kamilkurach/mrburger/resources/IMG_20240722_085424.jpg

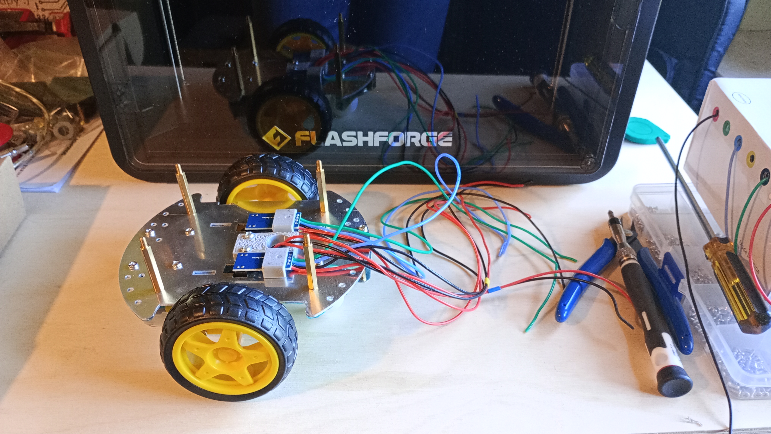
resources/IMG_20240722_085424.jpg
