kamilkurach/mrburger/resources/IMG_20240728_142720.jpg

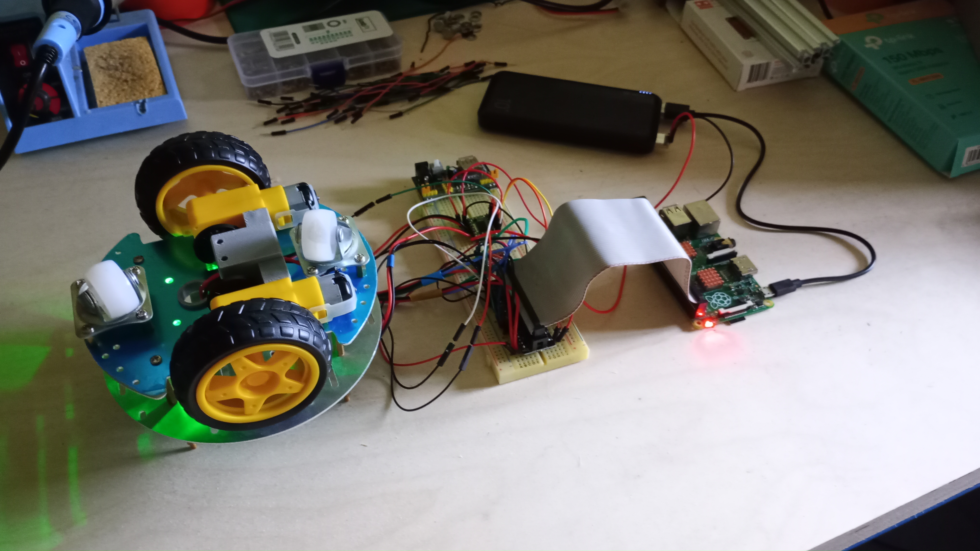
resources/IMG_20240728_142720.jpg
