kamilkurach/mrburger/resources/IMG_20240803_034906_3.jpg

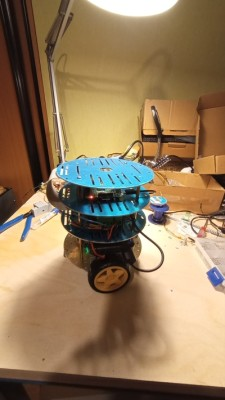
resources/IMG_20240803_034906_3.jpg
