kamilkurach/mrburger/resources/IMG_20240809_184807.jpg

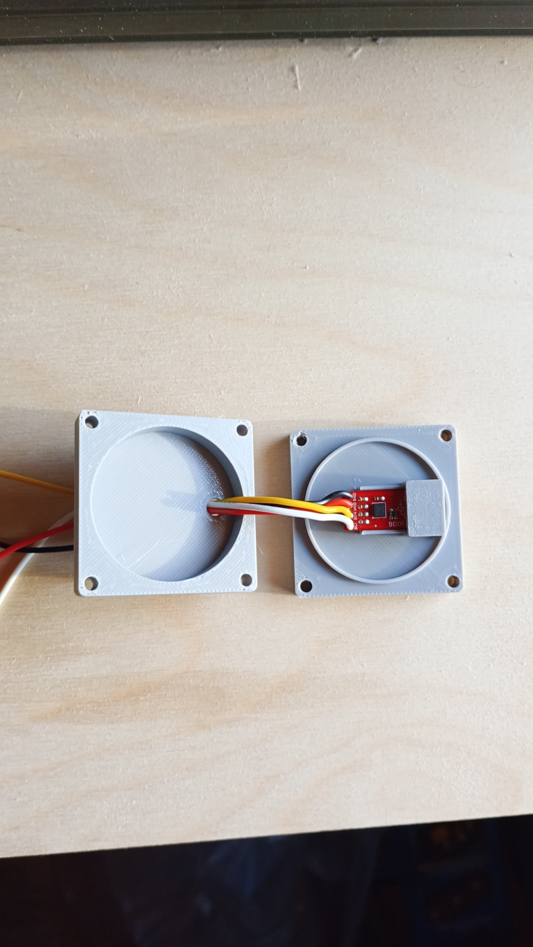
resources/IMG_20240809_184807.jpg
