kamilkurach/mrburger/resources/IMG_20241116_030415.jpg

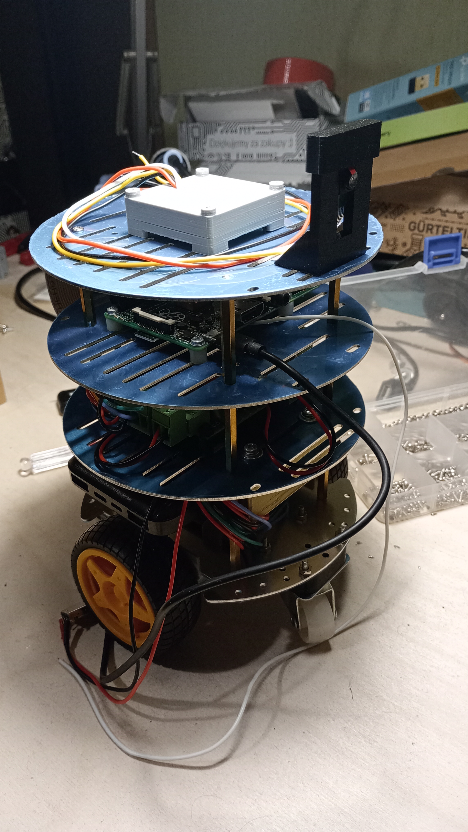
resources/IMG_20241116_030415.jpg
