kamilkurach/mrburger/resources/IMG_20241204_015451.jpg

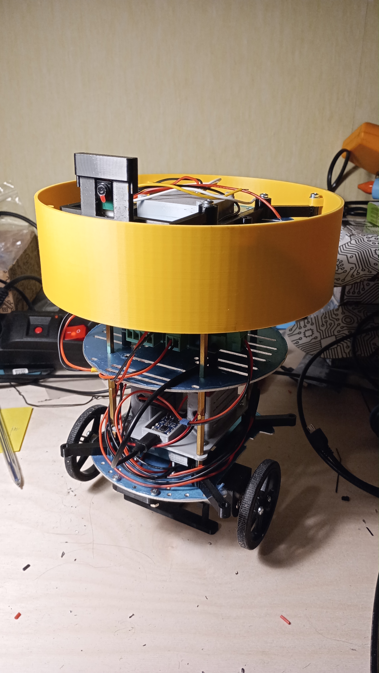
resources/IMG_20241204_015451.jpg
