kamilkurach/mrburger/resources/IMG_20241213_023858.jpg

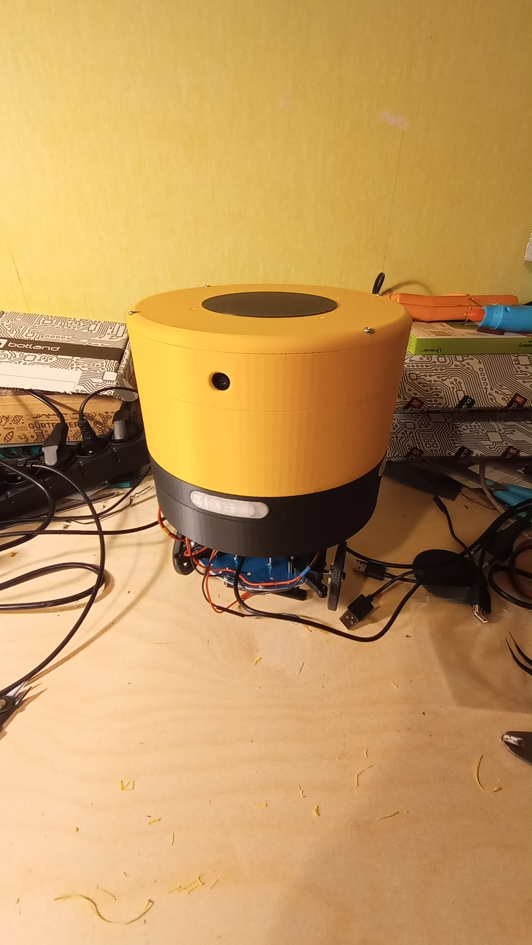
resources/IMG_20241213_023858.jpg
