kamilkurach/mrburger/resources/IMG_20241213_090648.jpg

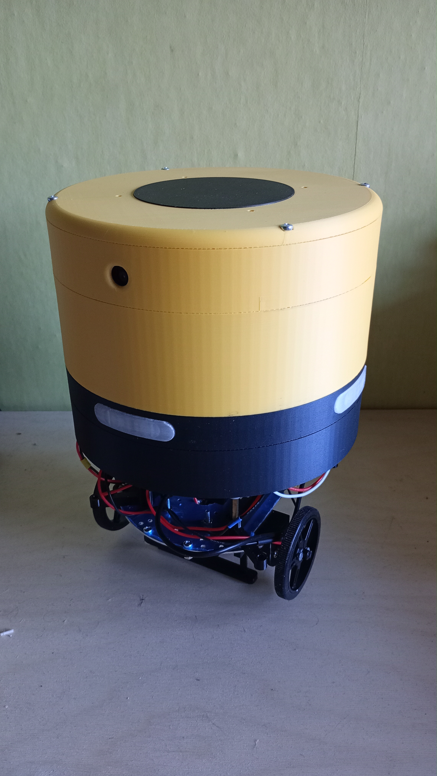
resources/IMG_20241213_090648.jpg
