kamilkurach/mrburger/stl/mrburger_induction_coil_bracket_coil_cover.stl

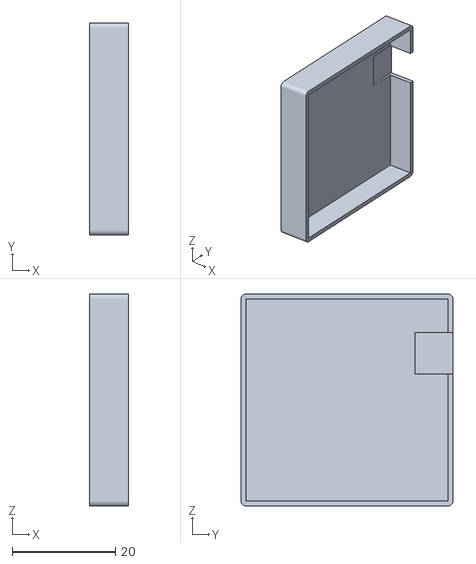
[picture p26: CAD file, 2024-12-05]
stl/mrburger_induction_coil_bracket_coil_cover.stl
7.50 x 41.0 x 41.0
