kamilkurach/mrburger/freecad/mrburger_bottom_hat.FCStd

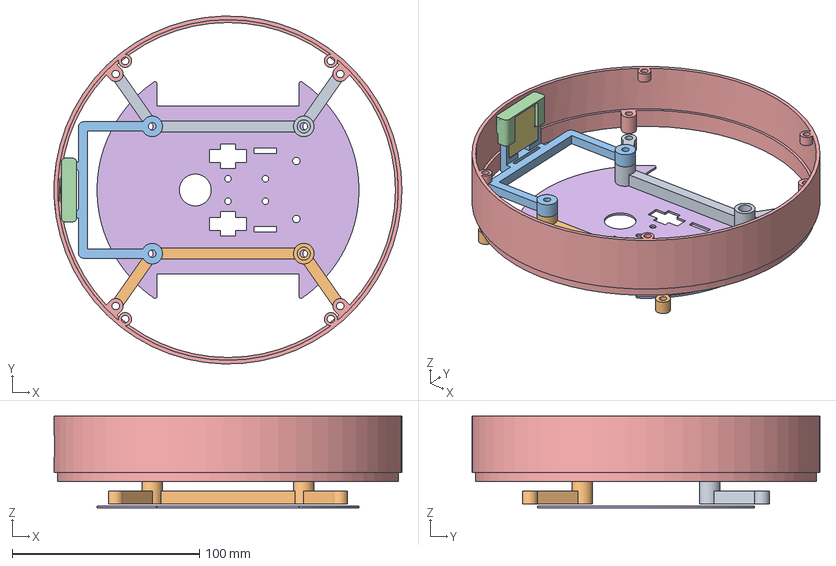
[picture p27: CAD file, 2024-12-08]
freecad/mrburger_bottom_hat.FCStd
186.0 x 185.9 x 49.0 mm
bracket
bracket_2
camera_bracket
clip
bottom_hat
mrburger_bottom_plate
mrburger_camera_module
