kamilkurach/mrburger/stl/mrburger_induction_coil_bracket_electronics_cover.stl

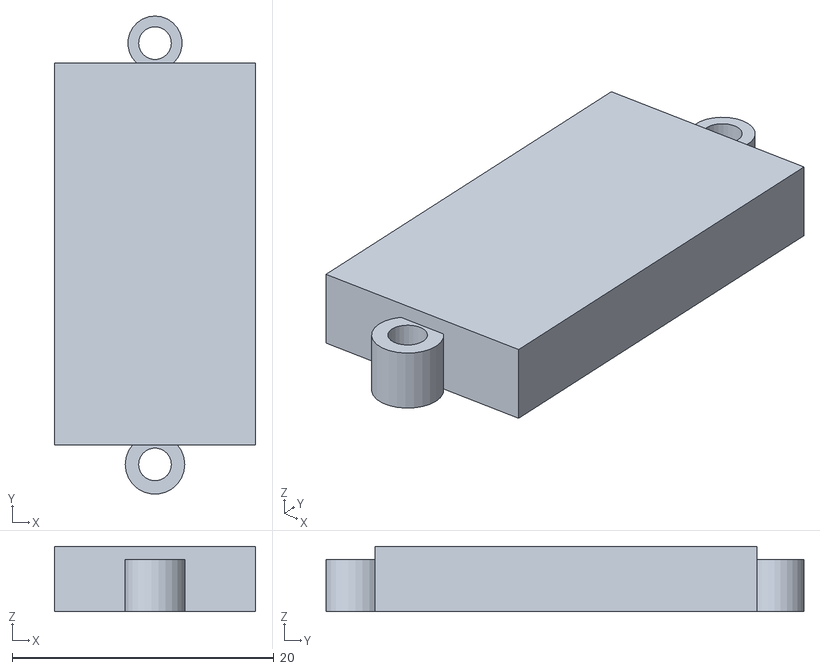
[picture p28: CAD file, 2024-12-05]
stl/mrburger_induction_coil_bracket_electronics_cover.stl
15.4 x 36.5 x 5.00
