kamilkurach/mrburger/freecad/mrburger_mid_ring.FCStd

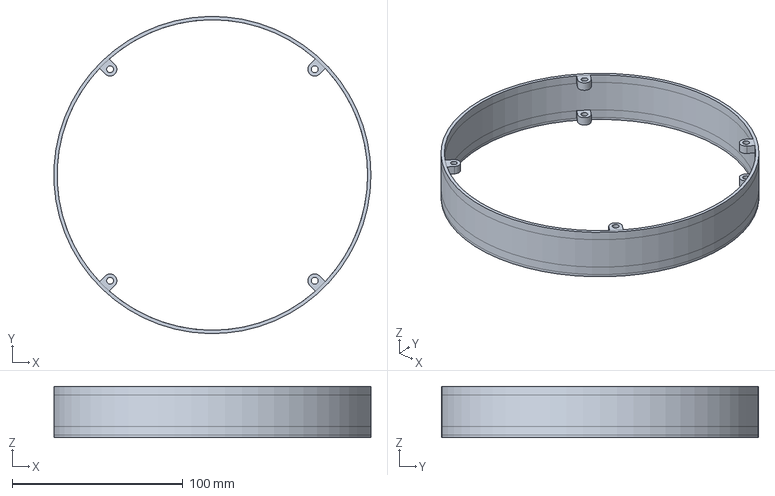
[picture p29: CAD file, 2024-12-06]
freecad/mrburger_mid_ring.FCStd
185.9 x 185.9 x 30.0 mm
