kamilkurach/mrburger/stl/mrburger_induction_coil_bracket_distance_tube.stl

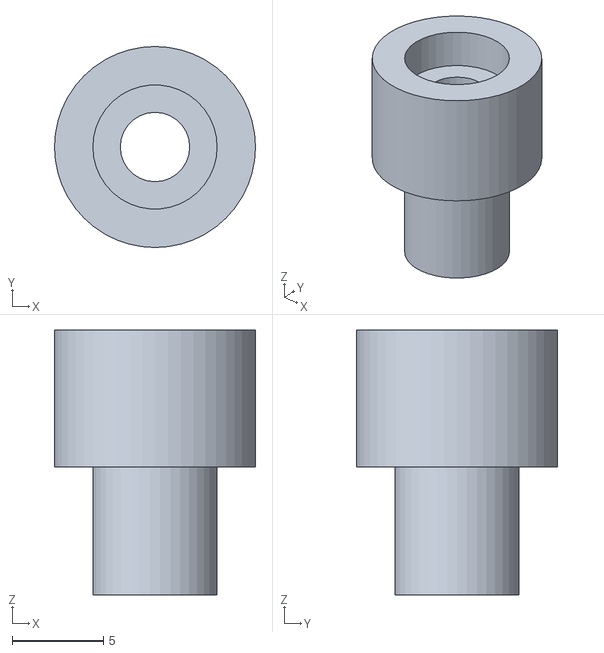
[picture p30: CAD file, 2024-12-05]
stl/mrburger_induction_coil_bracket_distance_tube.stl
11.0 x 11.0 x 14.5
