kamilkurach/mrburger/freecad/mrburger_induction_coil_bracke_2.FCStd

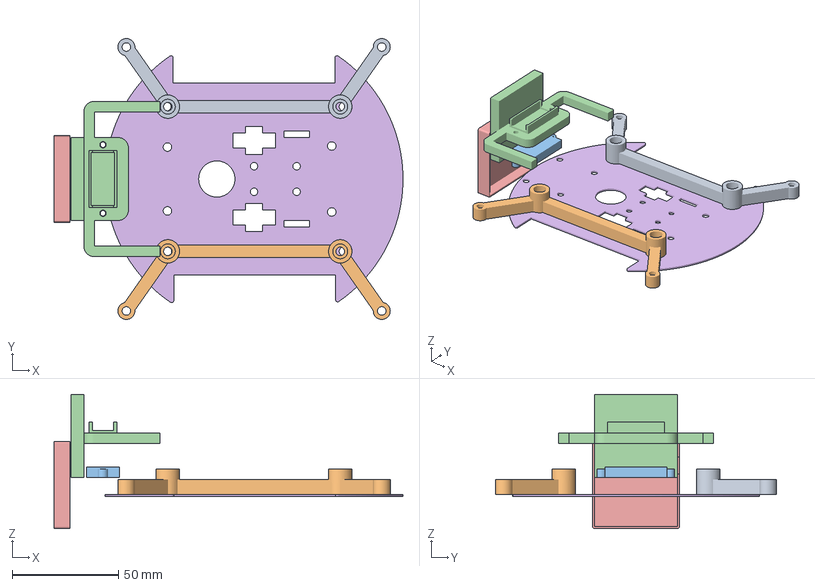
[picture p31: CAD file, 2024-12-05]
freecad/mrburger_induction_coil_bracke_2.FCStd
164.0 x 132.0 x 63.0 mm
bracket
bracket_2
electronics_cover
coil_bracket
coil_cover
mrburger_bottom_plate
