kamilkurach/mrburger/stl/mrburger_Li-Po_power_tray-pocket_w_vents.stl

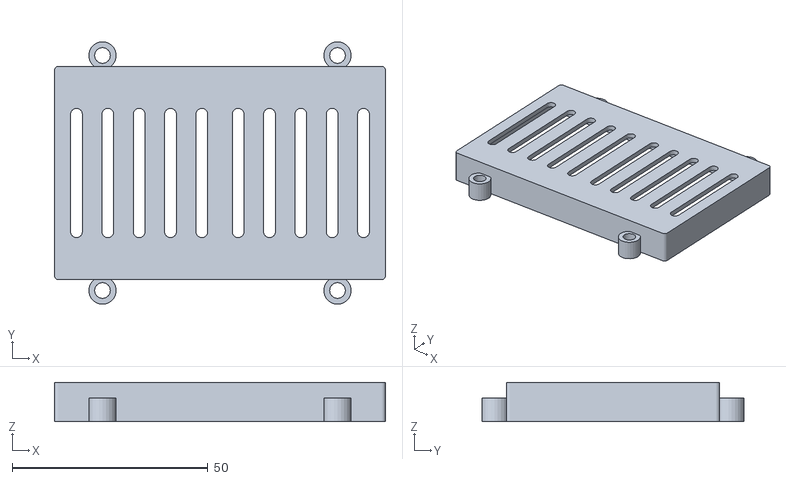
[picture p32: CAD file, 2024-12-03]
stl/mrburger_Li-Po_power_tray-pocket_w_vents.stl
84.5 x 67.0 x 10.0
