kamilkurach/mrburger/freecad/mrburger_induction_coil_bracket.FCStd

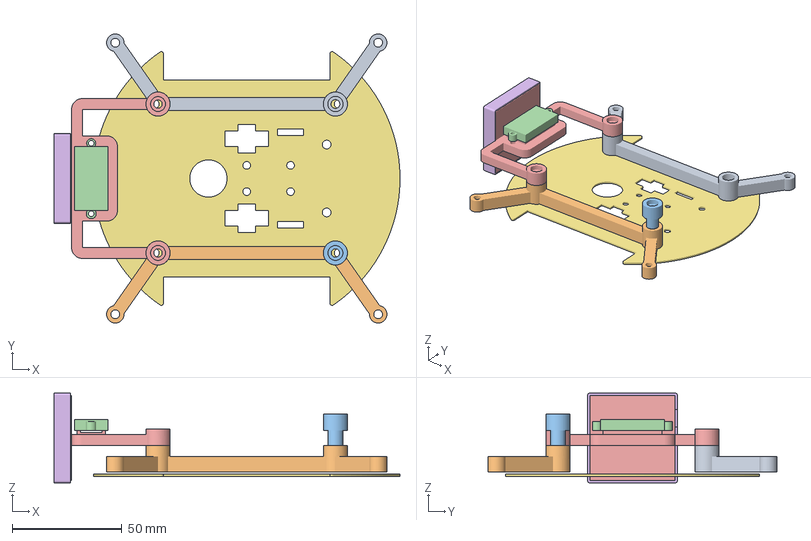
[picture p33: CAD file, 2024-12-05]
freecad/mrburger_induction_coil_bracket.FCStd
158.0 x 132.0 x 41.0 mm
bracket
bracket_2
bracket_distance_tube
electronics_cover
coil_bracket
coil_cover
mrburger_bottom_plate
