kamilkurach/mrburger/stl/mrburger_camera_bracket_clip.stl

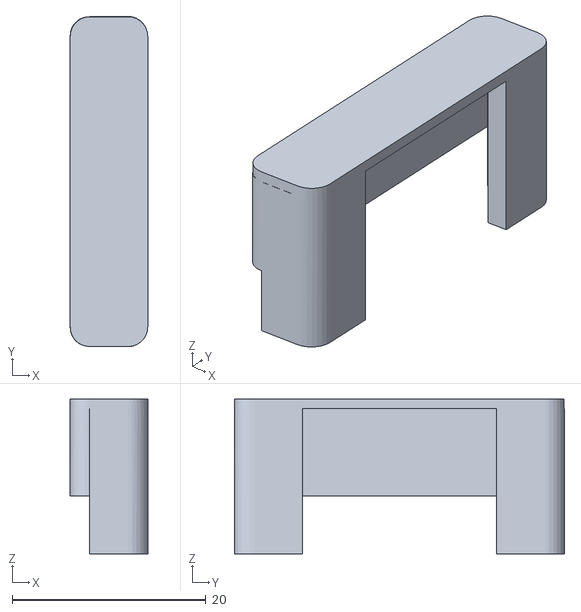
[picture p34: CAD file, 2024-12-02]
stl/mrburger_camera_bracket_clip.stl
8.00 x 34.1 x 16.0
