kamilkurach/mrburger/freecad/mrburger_tray.FCStd

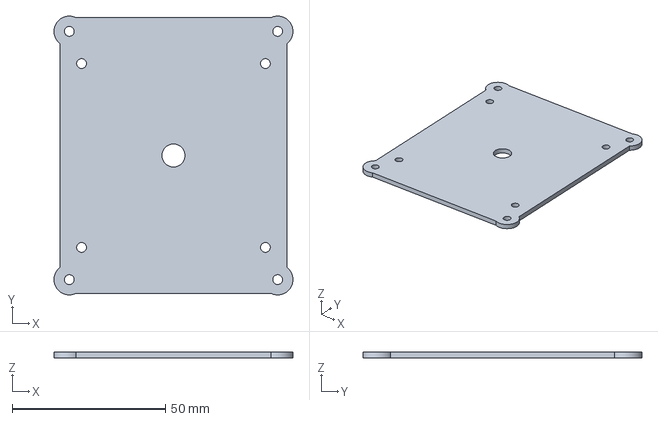
[picture p35: CAD file, 2024-12-04]
freecad/mrburger_tray.FCStd
78.0 x 91.0 x 2.00 mm
