kamilkurach/mrburger/stl/mrburger_powerbank_usb_connector_top.stl

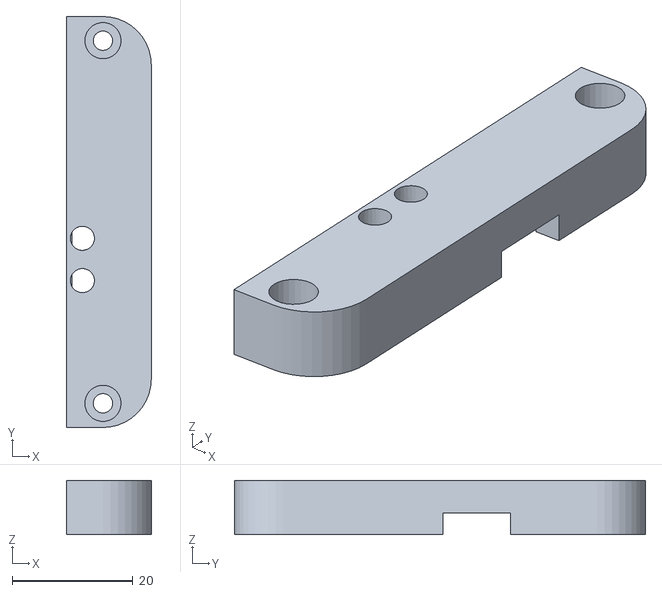
[picture p36: CAD file, 2024-11-28]
stl/mrburger_powerbank_usb_connector_top.stl
14.0 x 68.0 x 9.00
