kamilkurach/mrburger/freecad/mrburger_Li-Po_power_tray.FCStd

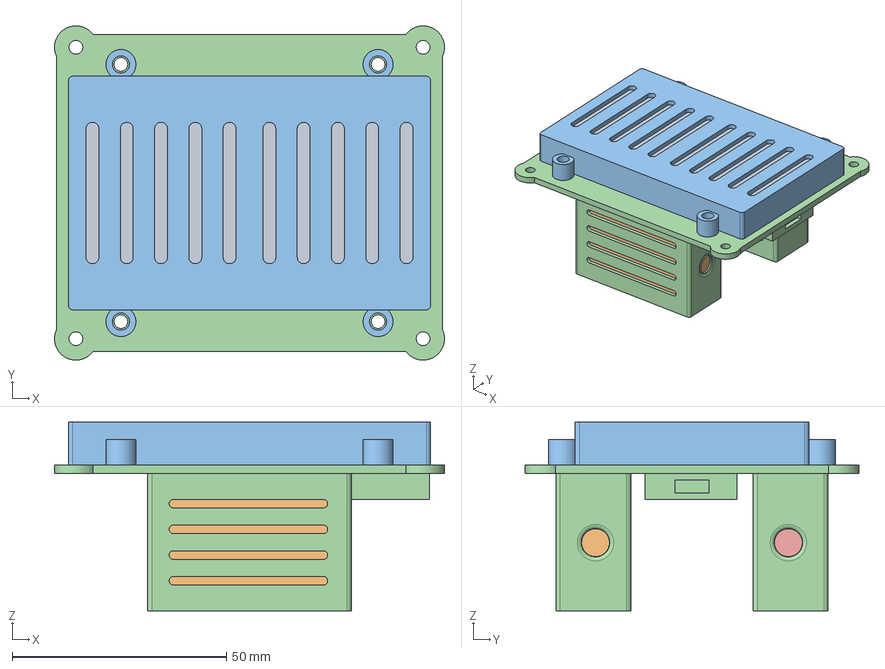
[picture p37: CAD file, 2024-12-03]
freecad/mrburger_Li-Po_power_tray.FCStd
91.0 x 78.0 x 44.0 mm
bat_3.7v_4000mAh_bbox
LM2577_bbox
pocket_w_vents
Zawartość003
LM2577_bbox001
