kamilkurach/mrburger/stl/mrburger_powerbank_usb_connector_bottom.stl

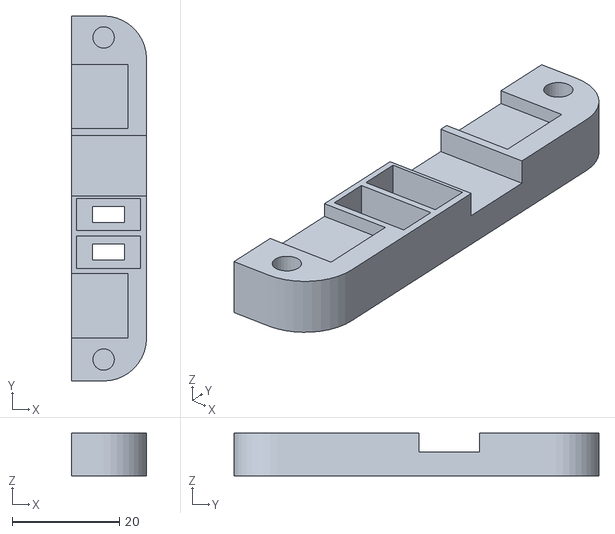
[picture p38: CAD file, 2024-11-28]
stl/mrburger_powerbank_usb_connector_bottom.stl
14.0 x 68.0 x 8.00
