kamilkurach/mrburger/freecad/mrburger_tmp_camera_holder.FCStd

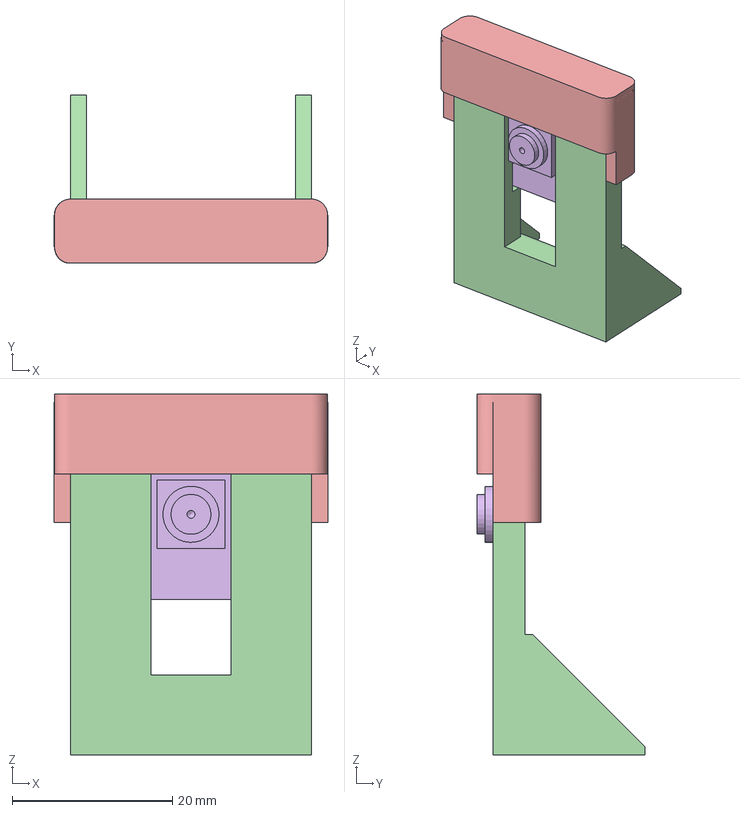
[picture p39: CAD file, 2024-12-02]
freecad/mrburger_tmp_camera_holder.FCStd
34.1 x 21.0 x 45.0 mm
Zawartość
camera_holder
clip
mrburger_camera_module
