kamilkurach/mrburger/stl/mrburger_mrburger_holder_support_point_3.stl

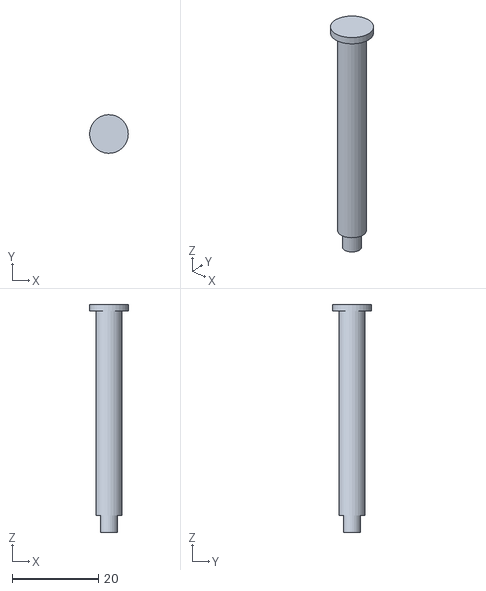
[picture p40: CAD file, 2024-11-27]
stl/mrburger_mrburger_holder_support_point_3.stl
8.98 x 8.99 x 53.0
