kamilkurach/mrburger/freecad/mrburger_camera_bracket.FCStd

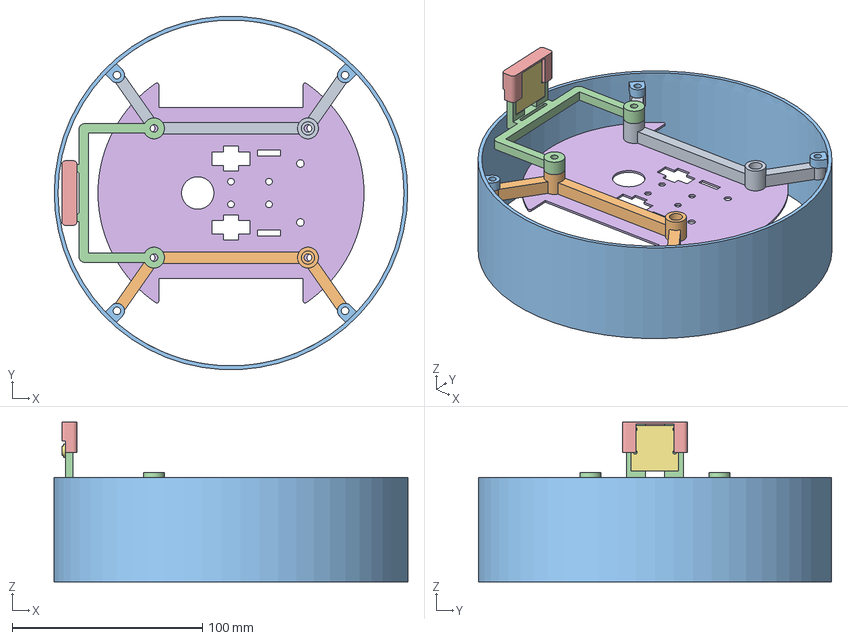
[picture p41: CAD file, 2024-12-02]
freecad/mrburger_camera_bracket.FCStd
186.0 x 185.7 x 84.0 mm
bracket
bracket_2
top_yellow_ring
camera_bracket
clip
mrburger_bottom_plate
mrburger_camera_module
