kamilkurach/mrburger/stl/mrburger_mrburger_holder_connector.stl

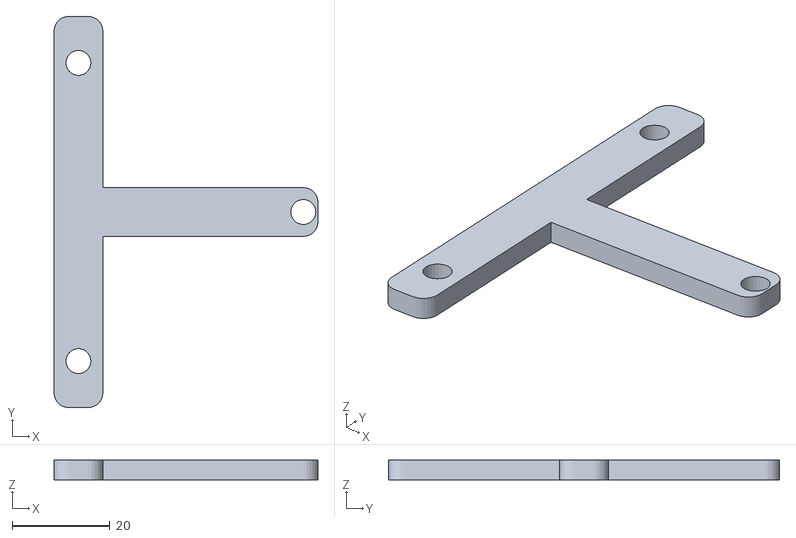
[picture p42: CAD file, 2024-11-25]
stl/mrburger_mrburger_holder_connector.stl
54.0 x 80.0 x 4.00
