kamilkurach/mrburger/freecad/mrburger_ring_2.FCStd

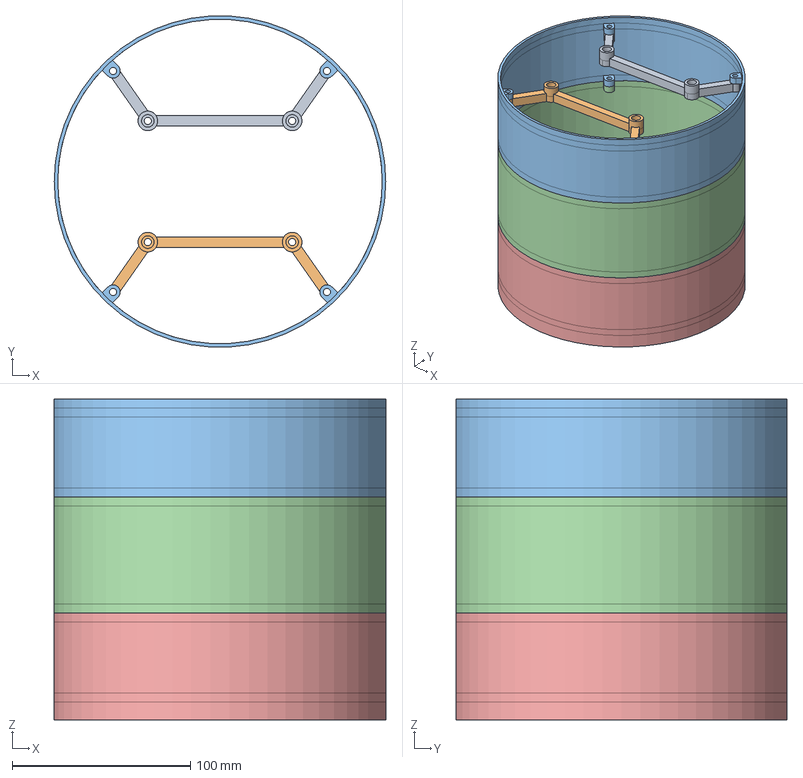
[picture p43: CAD file, 2024-12-01]
freecad/mrburger_ring_2.FCStd
186.0 x 185.7 x 180.0 mm
bracket
bracket_2
top_yellow_ring
mid_black_ring
bottom_yellow_ring
