kamilkurach/mrburger/stl/mrburger_mrburger_holder_support_point_1.stl

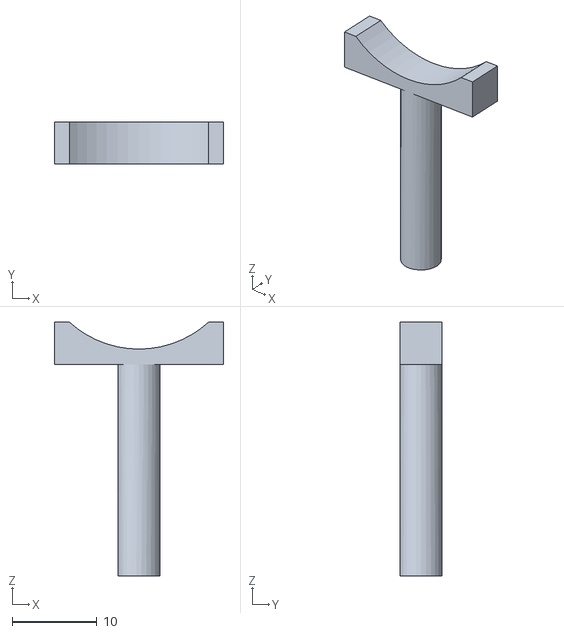
[picture p44: CAD file, 2024-11-25]
stl/mrburger_mrburger_holder_support_point_1.stl
20.0 x 5.00 x 30.0
