kamilkurach/mrburger/freecad/mrburger_top_bracket_2.FCStd

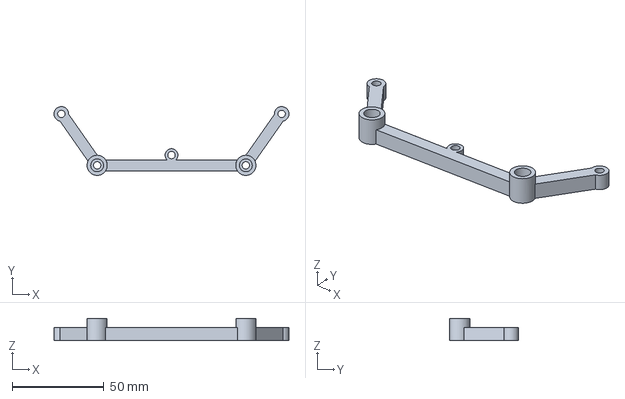
[picture p45: CAD file, 2024-12-01]
freecad/mrburger_top_bracket_2.FCStd
128.0 x 37.5 x 12.0 mm
