kamilkurach/mrburger/freecad/mrburger_bracket_2.FCStd

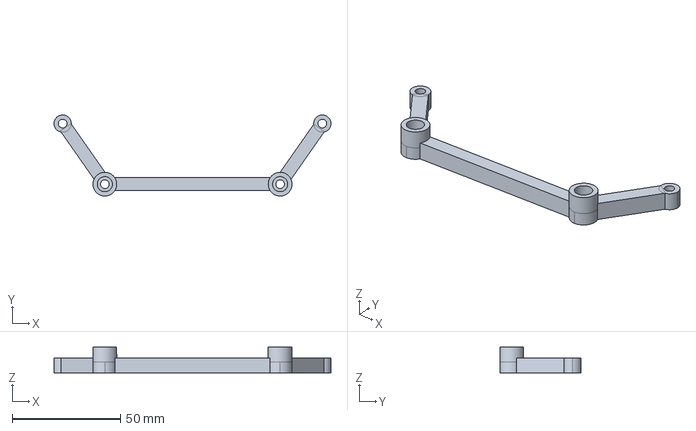
[picture p46: CAD file, 2024-11-30]
freecad/mrburger_bracket_2.FCStd
128.0 x 37.5 x 12.0 mm
