kamilkurach/mrburger/stl/mrburger_motor_holder_60:1_6v_clamp.stl

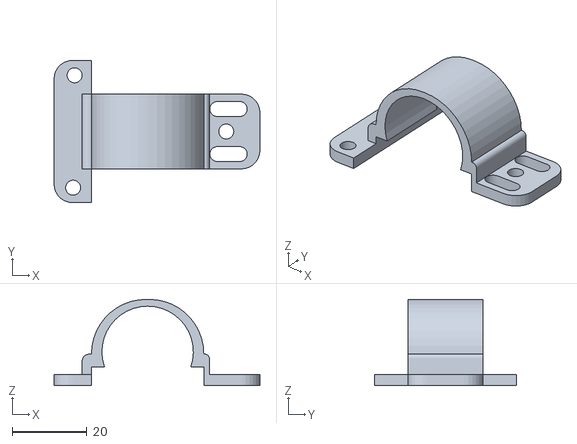
[picture p47: CAD file, 2024-11-25]
stl/mrburger_motor_holder_60:1_6v_clamp.stl
55.0 x 38.0 x 23.0
