kamilkurach/mrburger/freecad/mrburger_ring.FCStd

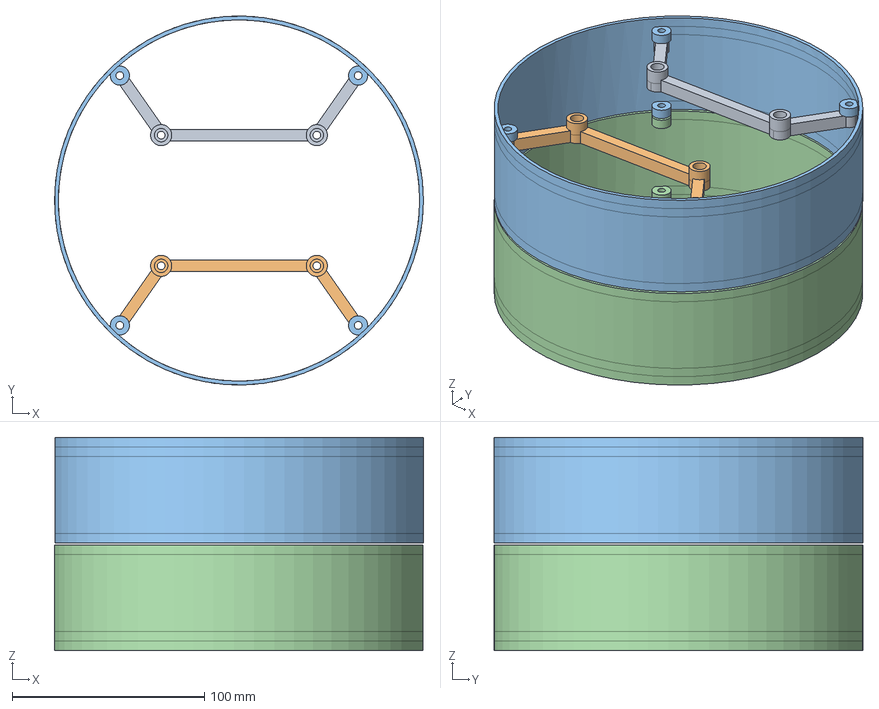
[picture p48: CAD file, 2024-11-30]
freecad/mrburger_ring.FCStd
192.0 x 191.9 x 111.0 mm
bracket
bracket_2
top_yellow_ring
mid_black_ring
