kamilkurach/mrburger/stl/mrburger_motor_holder_60:1_6v.stl

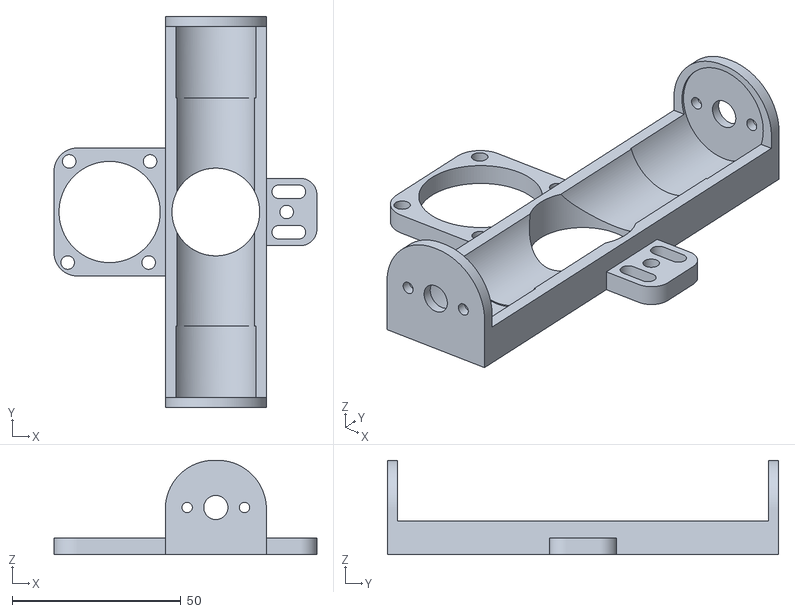
[picture p49: CAD file, 2024-11-24]
stl/mrburger_motor_holder_60:1_6v.stl
78.0 x 116.0 x 28.0
