kamilkurach/mrburger/freecad/mrburger_mid_bracket.FCStd

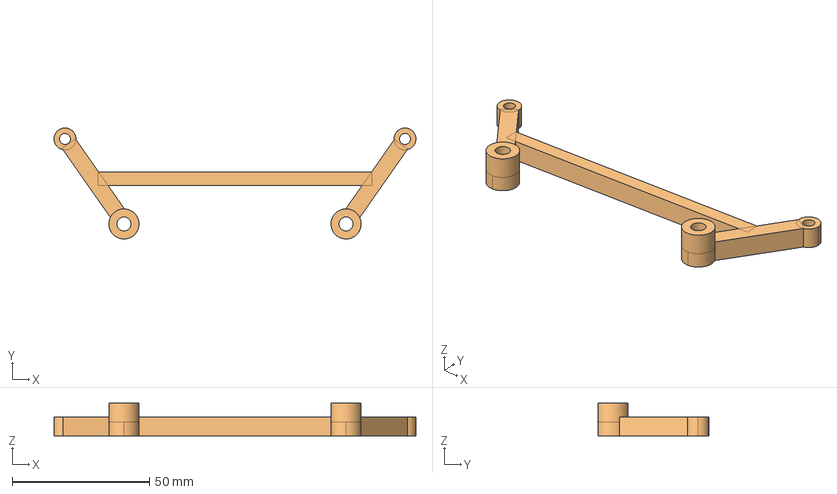
[picture p50: CAD file, 2024-11-29]
freecad/mrburger_mid_bracket.FCStd
132.0 x 40.5 x 12.0 mm
Tube014
