kamilkurach/mrburger/stl/mrburger_ultrasonic_sensor_ring.stl

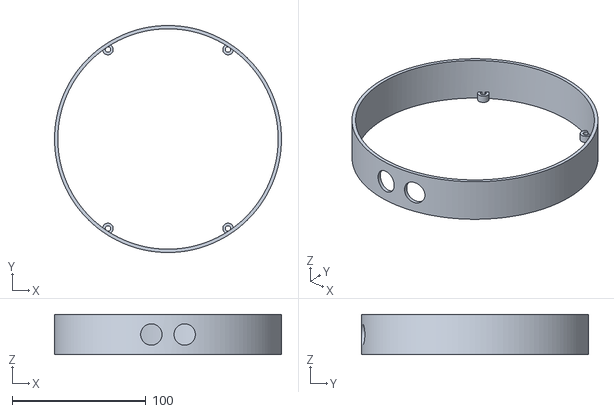
[picture p51: CAD file, 2024-11-22]
stl/mrburger_ultrasonic_sensor_ring.stl
170.0 x 169.9 x 30.0
