kamilkurach/mrburger/freecad/mrburger_powerbank_usb_connector.FCStd

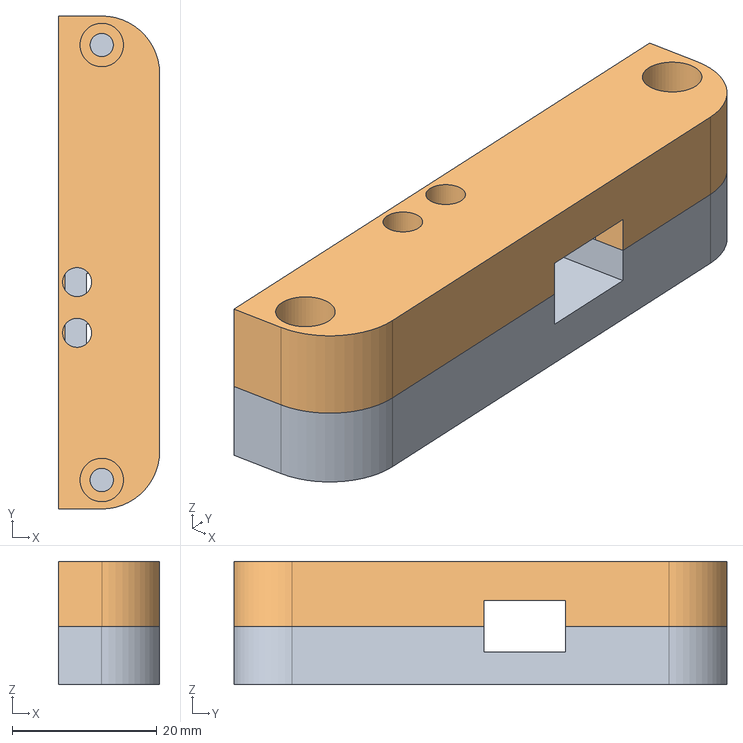
[picture p52: CAD file, 2024-11-28]
freecad/mrburger_powerbank_usb_connector.FCStd
14.0 x 68.0 x 17.0 mm
bottom
top
