kamilkurach/mrburger/stl/mrburger_turn_signal_ring.stl

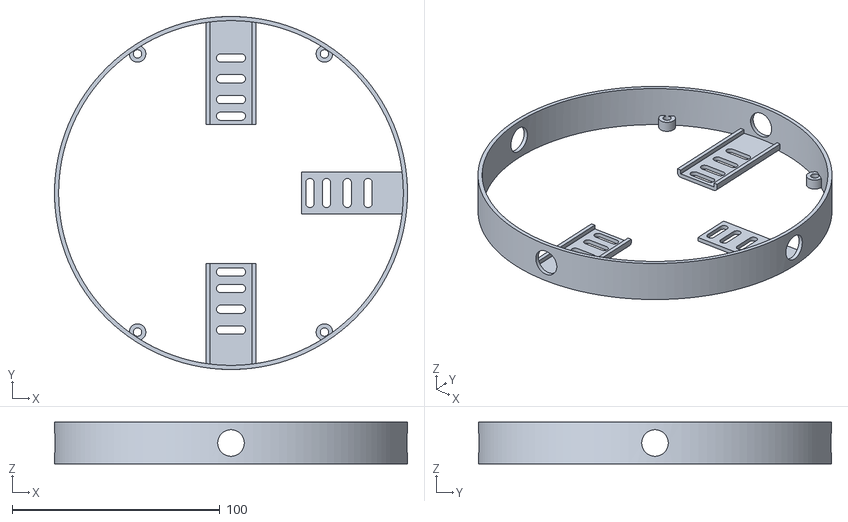
[picture p53: CAD file, 2024-11-22]
stl/mrburger_turn_signal_ring.stl
170.0 x 170.0 x 20.0
