kamilkurach/mrburger/freecad/mrburger_test_stand.FCStd

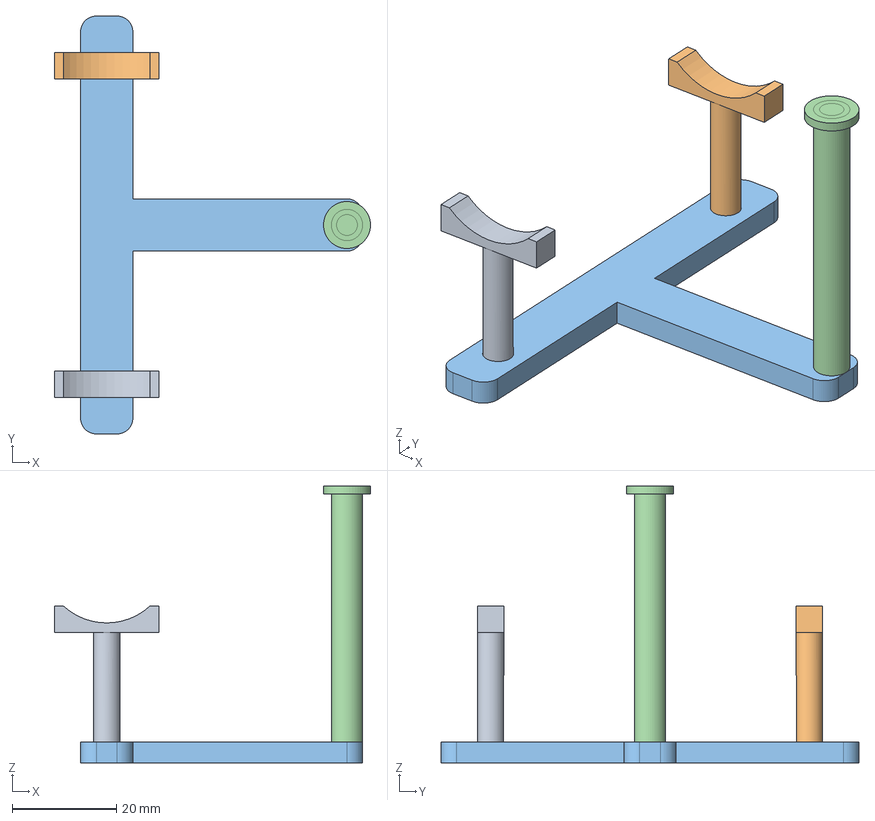
[picture p54: CAD file, 2024-11-27]
freecad/mrburger_test_stand.FCStd
60.5 x 80.0 x 53.0 mm
support_point_1
support_point_2
connector
support_point_3
