kamilkurach/mrburger/stl/mrburger_tmp_camera_holder-clip.stl

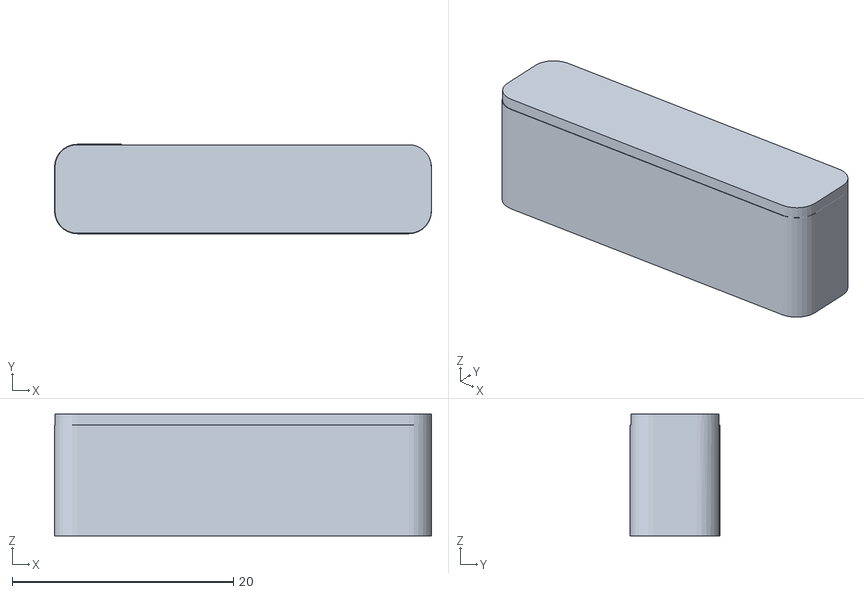
[picture p55: CAD file, 2024-11-15]
stl/mrburger_tmp_camera_holder-clip.stl
34.1 x 8.10 x 11.0
