kamilkurach/mrburger/freecad/mrburger_bracket.FCStd

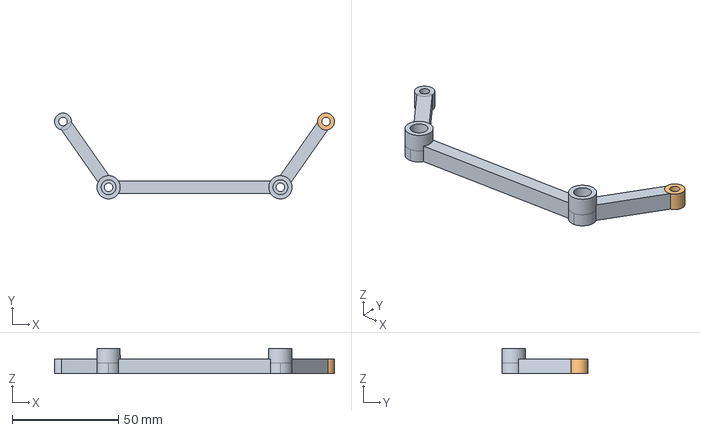
[picture p56: CAD file, 2024-11-27]
freecad/mrburger_bracket.FCStd
132.0 x 40.5 x 12.0 mm
bracket
Tube014
