kamilkurach/mrburger/stl/mrburger_top_plate_for_printing.stl

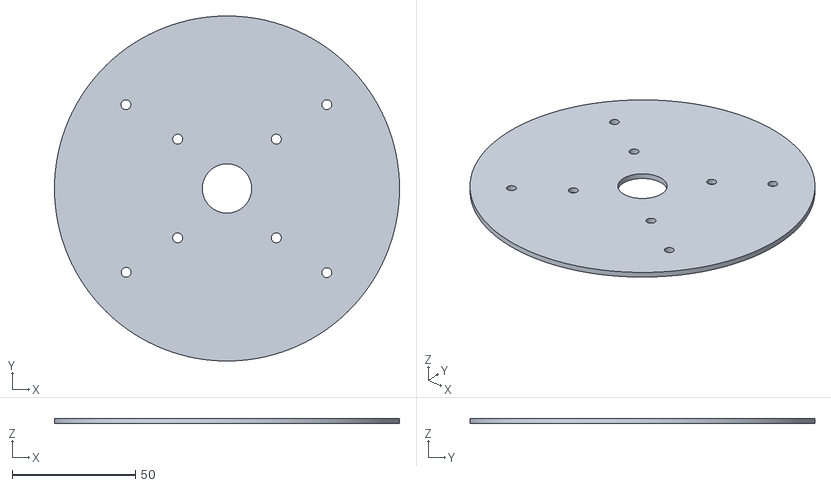
[picture p57: CAD file, 2024-08-13]
stl/mrburger_top_plate_for_printing.stl
140.0 x 140.0 x 2.20
