kamilkurach/mrburger/freecad/mrburger_tracer_powerbank_10000mAh.FCStd

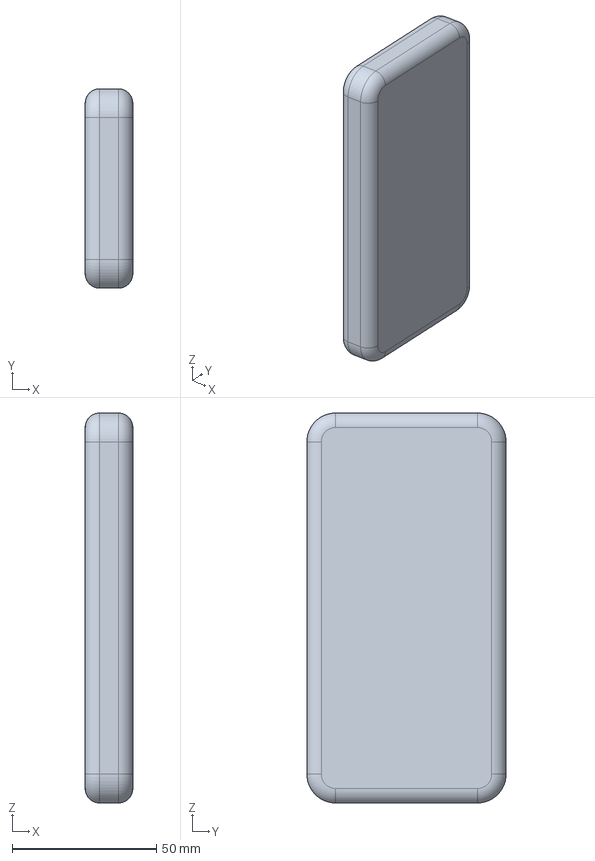
[picture p58: CAD file, 2024-11-26]
freecad/mrburger_tracer_powerbank_10000mAh.FCStd
16.5 x 69.0 x 135.0 mm
