kamilkurach/mrburger/stl/M3.5-tube.stl

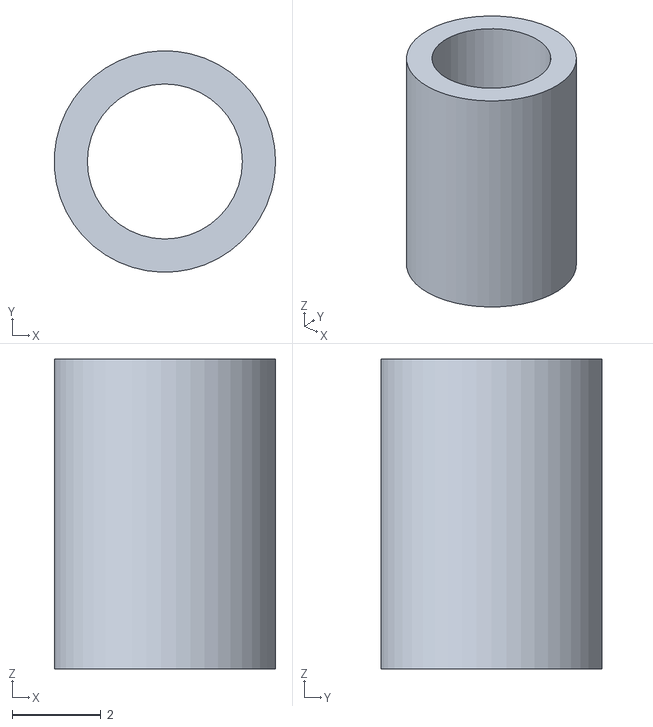
[picture p59: CAD file, 2024-08-09]
stl/M3.5-tube.stl
4.99 x 5.00 x 7.00
