kamilkurach/mrburger/freecad/mrburger_powerbank_holder.FCStd

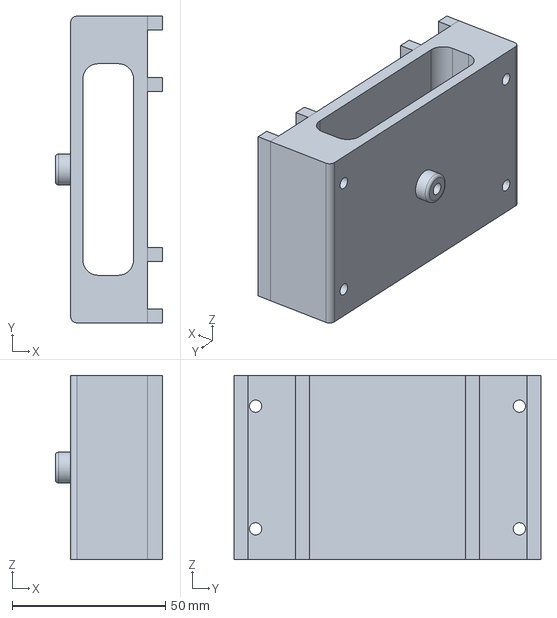
[picture p60: CAD file, 2024-11-26]
freecad/mrburger_powerbank_holder.FCStd
35.0 x 100.0 x 60.0 mm
