kamilkurach/mrburger/stl/M3.5.stl

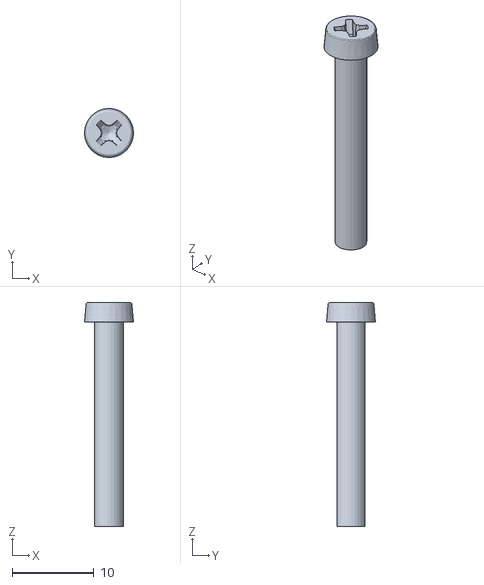
[picture p61: CAD file, 2024-08-09]
stl/M3.5.stl
6.00 x 5.97 x 27.4
