kamilkurach/mrburger/freecad/mrburger_wheel_spacer.FCStd

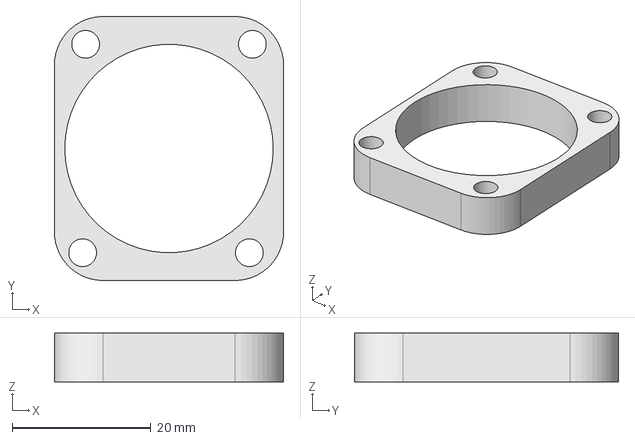
[picture p62: CAD file, 2024-11-25]
freecad/mrburger_wheel_spacer.FCStd
33.0 x 38.0 x 7.00 mm
