kamilkurach/mrburger/stl/mrburger_imu_mount_bottom_pin.stl

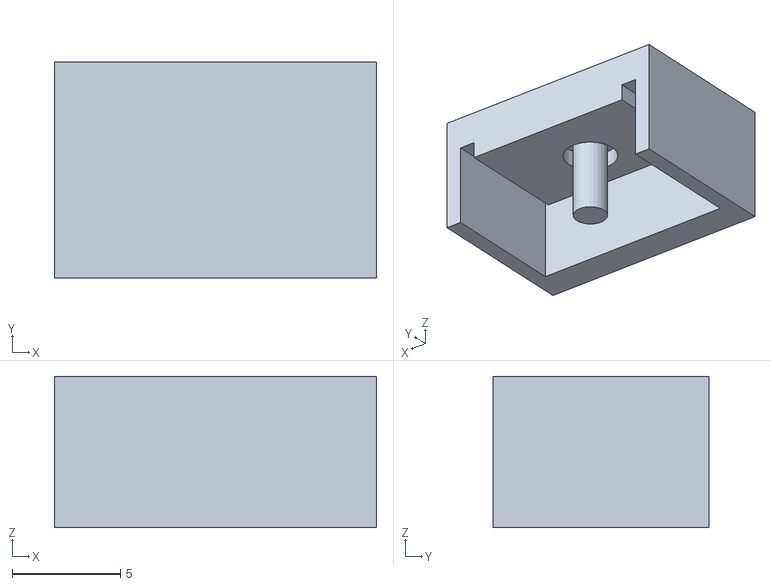
[picture p63: CAD file, 2024-08-09]
stl/mrburger_imu_mount_bottom_pin.stl
14.9 x 10.0 x 7.00
