kamilkurach/mrburger/freecad/mrburger_motor_holder_2.FCStd

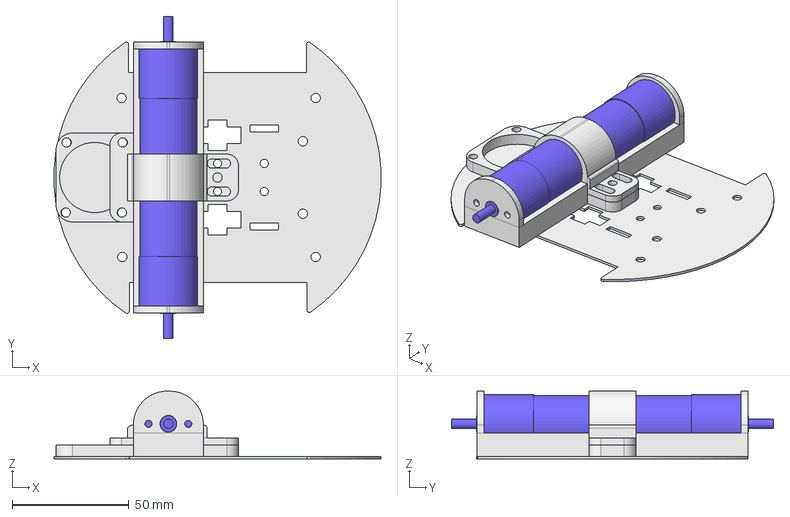
[picture p64: CAD file, 2024-11-25]
freecad/mrburger_motor_holder_2.FCStd
139.8 x 137.8 x 29.0 mm
bottom_plate
motor_holder_v2
motors
clamp
