kamilkurach/mrburger/stl/mrburger_imu_mount_top_cover.stl

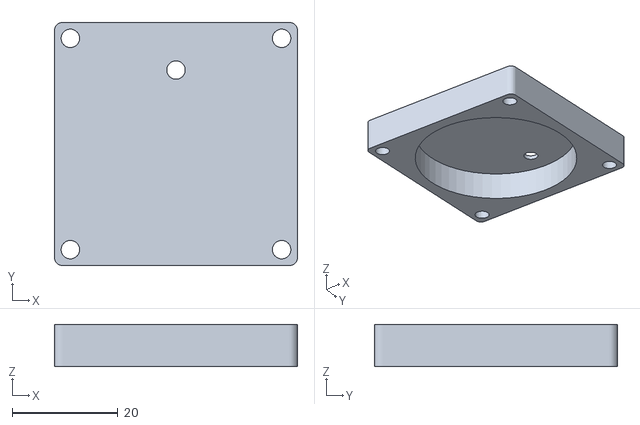
[picture p65: CAD file, 2024-08-08]
stl/mrburger_imu_mount_top_cover.stl
46.0 x 46.0 x 8.00
