kamilkurach/mrburger/freecad/mrburger_bottom_plate.FCStd

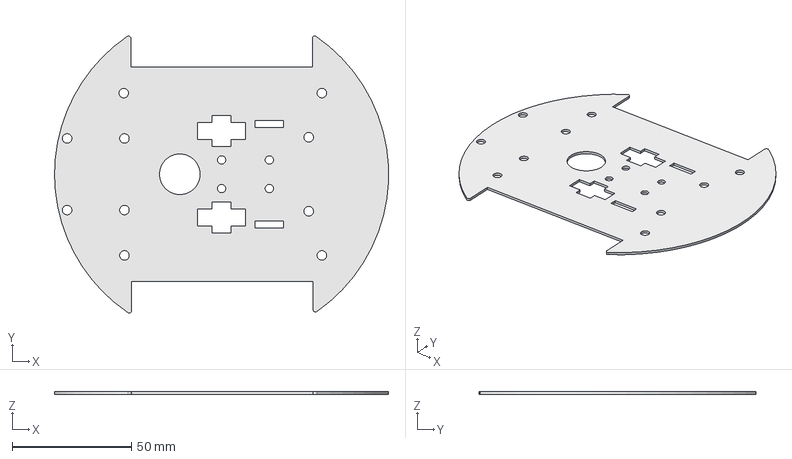
[picture p66: CAD file, 2024-11-23]
freecad/mrburger_bottom_plate.FCStd
139.9 x 116.0 x 1.10 mm
