kamilkurach/mrburger/stl/mrburger_imu_mount_bottom.stl

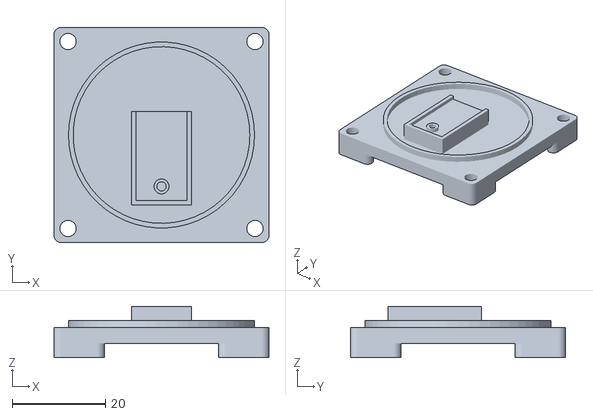
[picture p67: CAD file, 2024-08-08]
stl/mrburger_imu_mount_bottom.stl
46.0 x 46.0 x 11.0
