kamilkurach/mrburger/freecad/mrburger_ultrasonic_sensor.FCStd

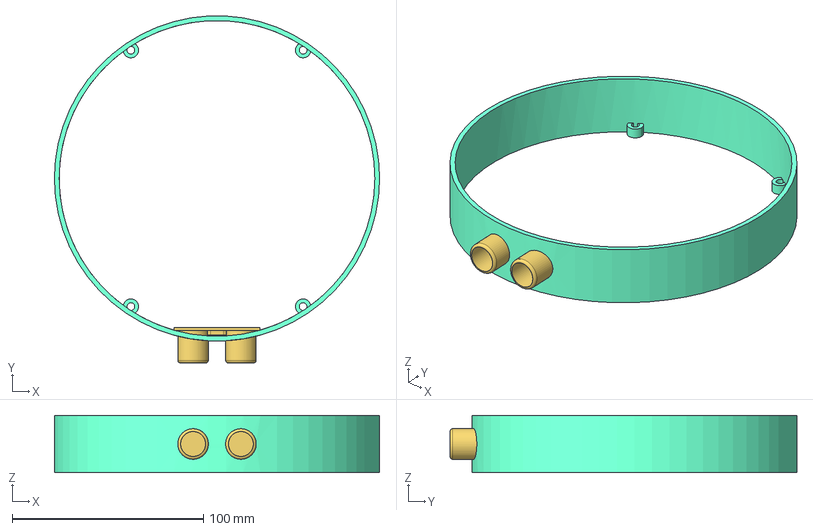
[picture p68: CAD file, 2024-11-22]
freecad/mrburger_ultrasonic_sensor.FCStd
170.0 x 181.4 x 30.0 mm
