kamilkurach/mrburger/freecad/mrburger_turn_signal.FCStd

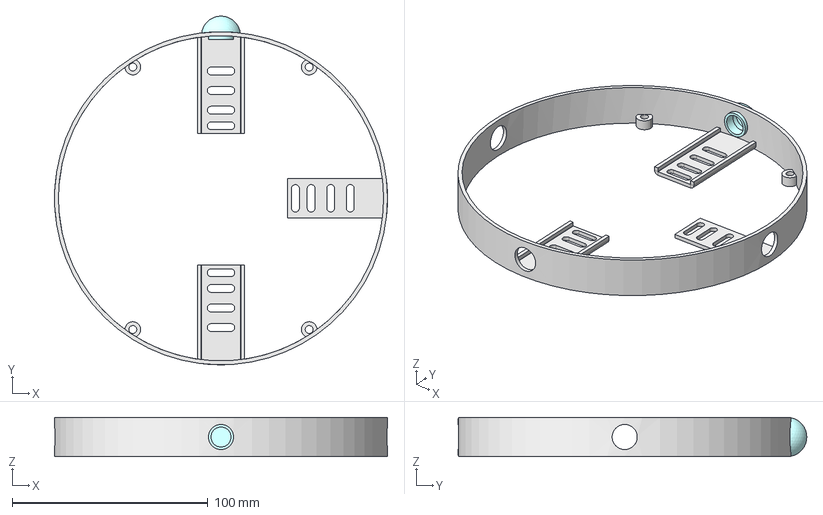
[picture p70: CAD file, 2024-11-22]
freecad/mrburger_turn_signal.FCStd
170.0 x 178.0 x 20.0 mm
turn_signal
ring
