kamilkurach/mrburger/stl/mrburger_motor_holder_3.stl

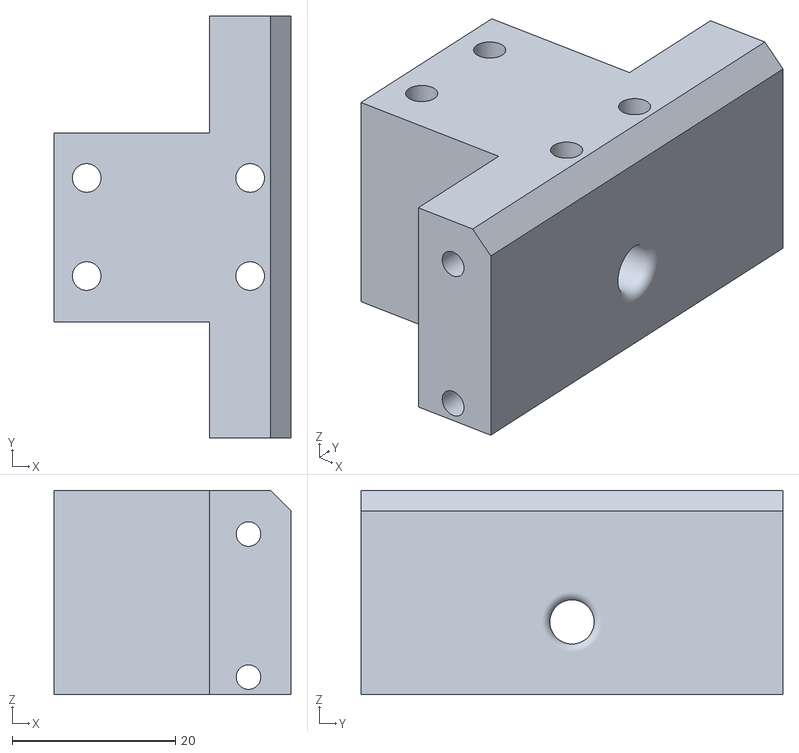
[picture p71: CAD file, 2024-07-29]
stl/mrburger_motor_holder_3.stl
29.0 x 51.6 x 25.0
