kamilkurach/mrburger/freecad/mrburger_led_ring.FCStd

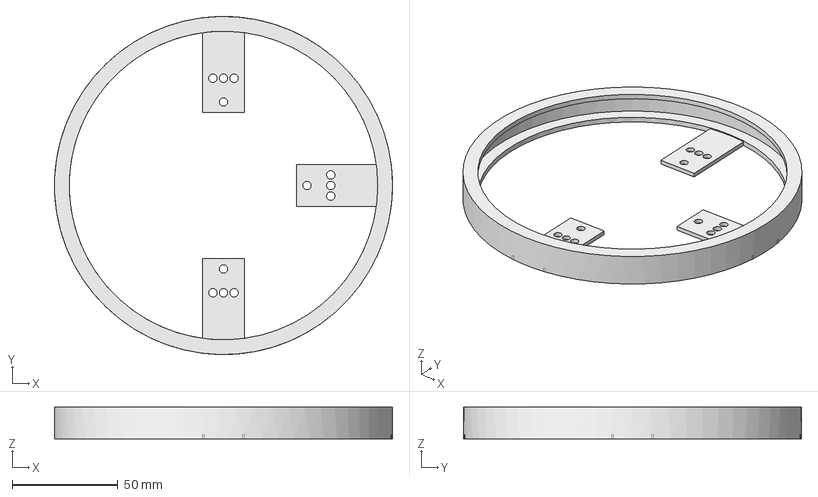
[picture p72: CAD file, 2024-11-21]
freecad/mrburger_led_ring.FCStd
160.0 x 159.9 x 15.0 mm
