kamilkurach/mrburger/stl/mrburger_sensor_holder_3.stl

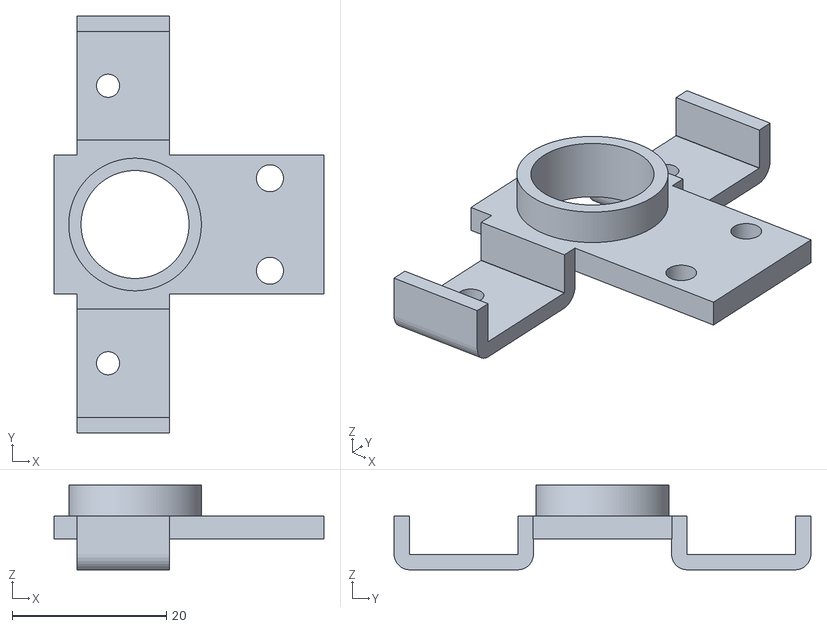
[picture p73: CAD file, 2024-07-23]
stl/mrburger_sensor_holder_3.stl
35.0 x 54.1 x 11.0
