kamilkurach/mrburger/freecad/mrburger_wheel_n_tire_test.FCStd

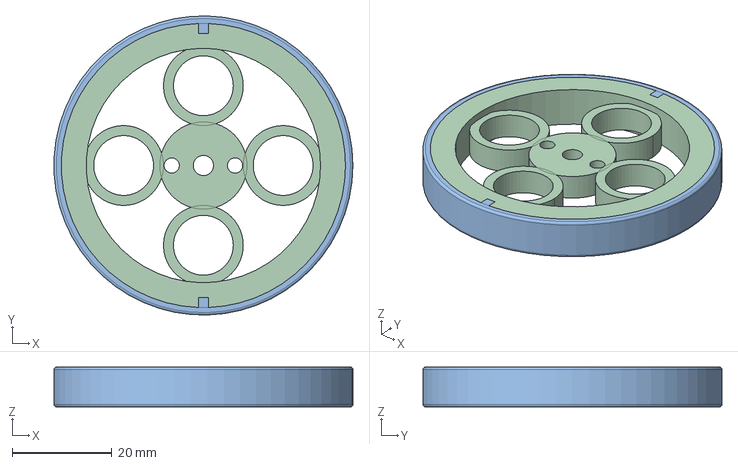
[picture p74: CAD file, 2024-11-21]
freecad/mrburger_wheel_n_tire_test.FCStd
60.0 x 60.0 x 8.00 mm
wheel
tire
