kamilkurach/mrburger/stl/mrburger_sensor_spacer.stl

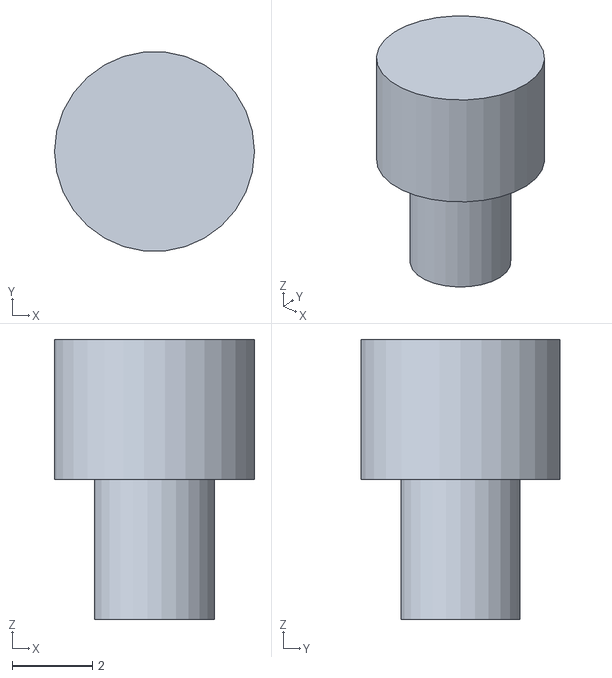
[picture p75: CAD file, 2024-07-21]
stl/mrburger_sensor_spacer.stl
5.00 x 4.97 x 7.00
