kamilkurach/mrburger/freecad/mrburger_motor_6v_60:1.FCStd

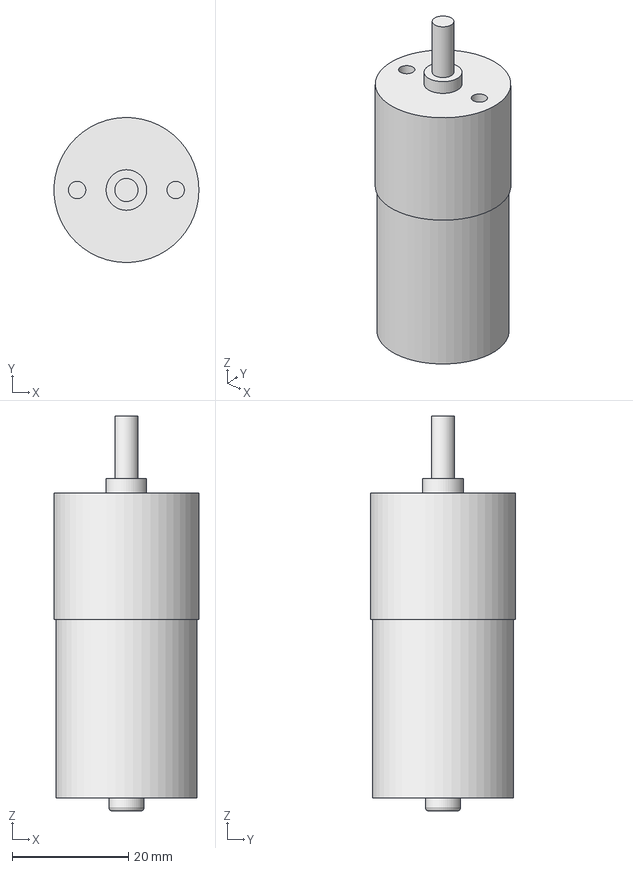
[picture p76: CAD file, 2024-11-20]
freecad/mrburger_motor_6v_60:1.FCStd
25.0 x 25.0 x 68.1 mm
