kamilkurach/mrburger/freecad/mrburger_motor_wheel_spacer.FCStd

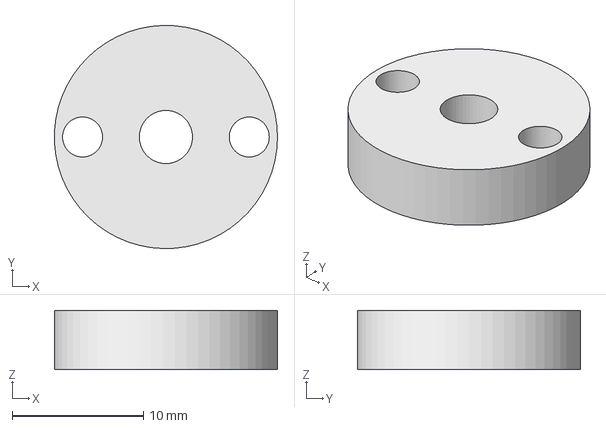
[picture p77: CAD file, 2024-11-20]
freecad/mrburger_motor_wheel_spacer.FCStd
17.0 x 17.0 x 4.50 mm
