kamilkurach/mrburger/freecad/mrburger_tmp_led_holder.FCStd

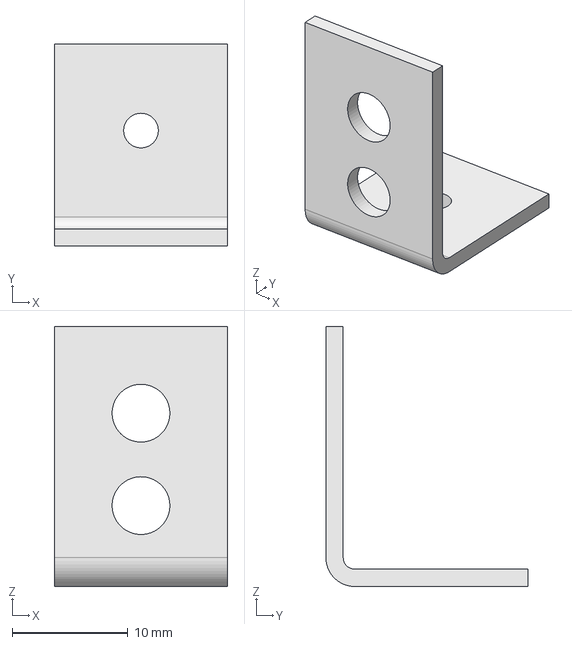
[picture p78: CAD file, 2024-11-19]
freecad/mrburger_tmp_led_holder.FCStd
15.0 x 17.5 x 22.5 mm
