kamilkurach/mrburger/freecad/mrburger_turn_signal_2.FCStd

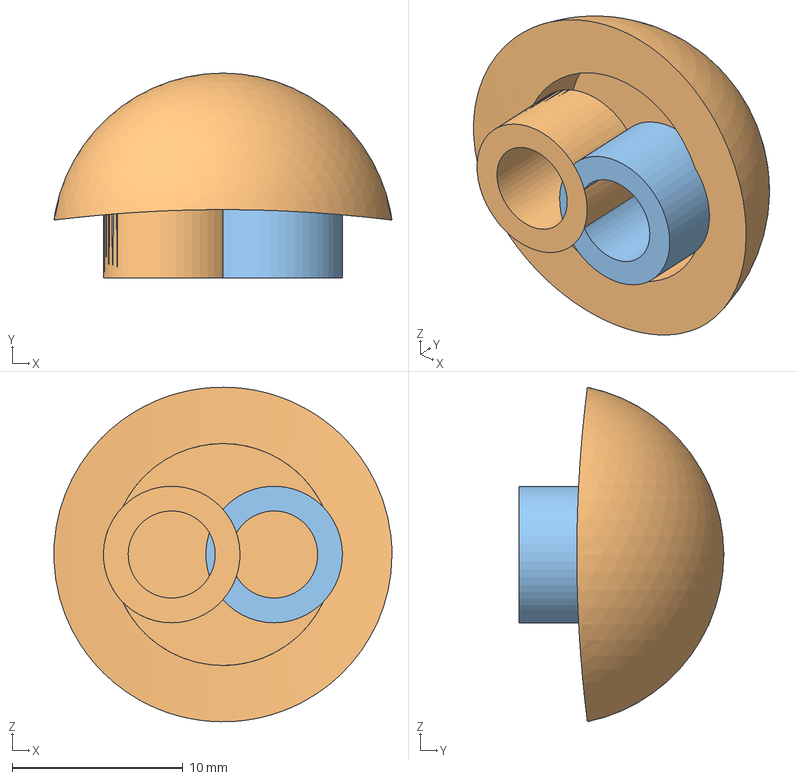
[picture p79: CAD file, 2024-11-19]
freecad/mrburger_turn_signal_2.FCStd
19.8 x 12.0 x 19.6 mm
Tube002
Tube003
