kamilkurach/mrburger/freecad/mrburger_wheel_spacer_n_extender.FCStd

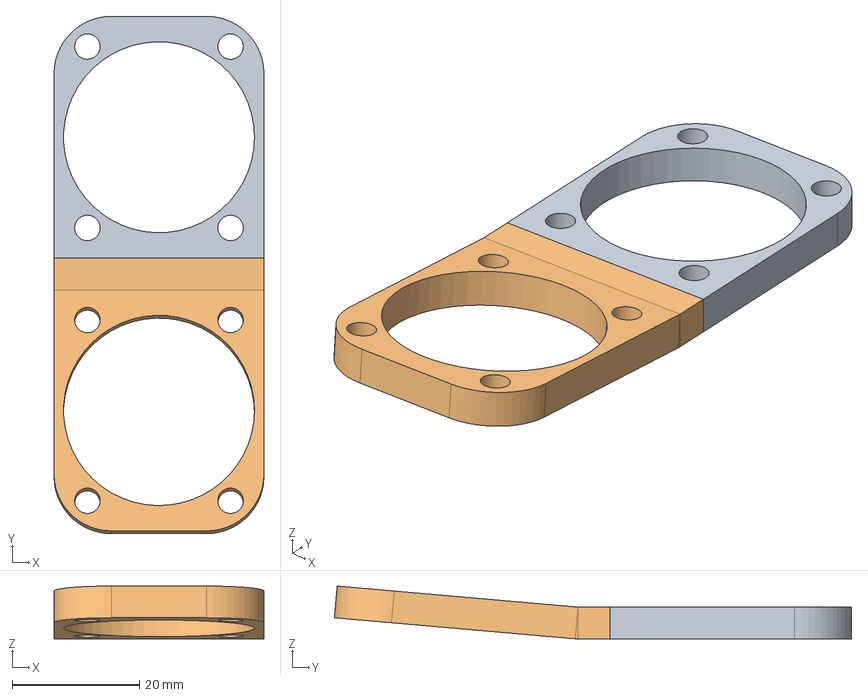
[picture p80: CAD file, 2024-11-18]
freecad/mrburger_wheel_spacer_n_extender.FCStd
33.0 x 81.3 x 8.31 mm
