kamilkurach/mrburger/freecad/mrburger_bottom.FCStd

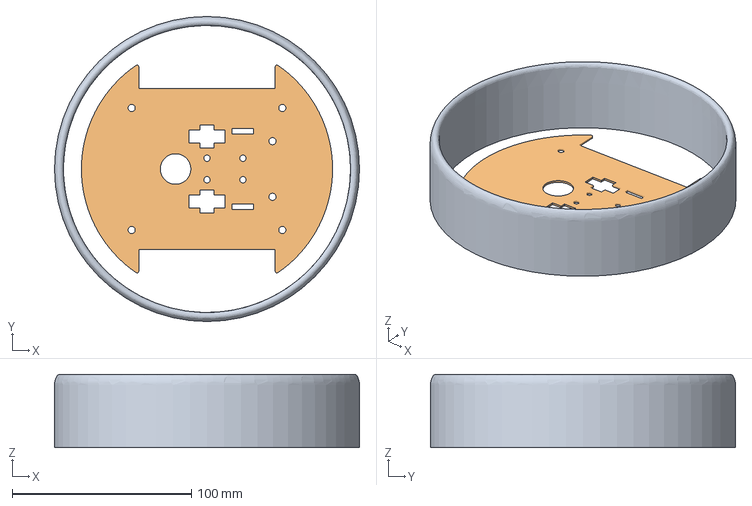
[picture p81: CAD file, 2024-08-25]
freecad/mrburger_bottom.FCStd
170.0 x 170.0 x 40.9 mm
Zawartość001
mrburger_bottom_plate
