kamilkurach/mrburger/freecad/mrburger_chassis.FCStd

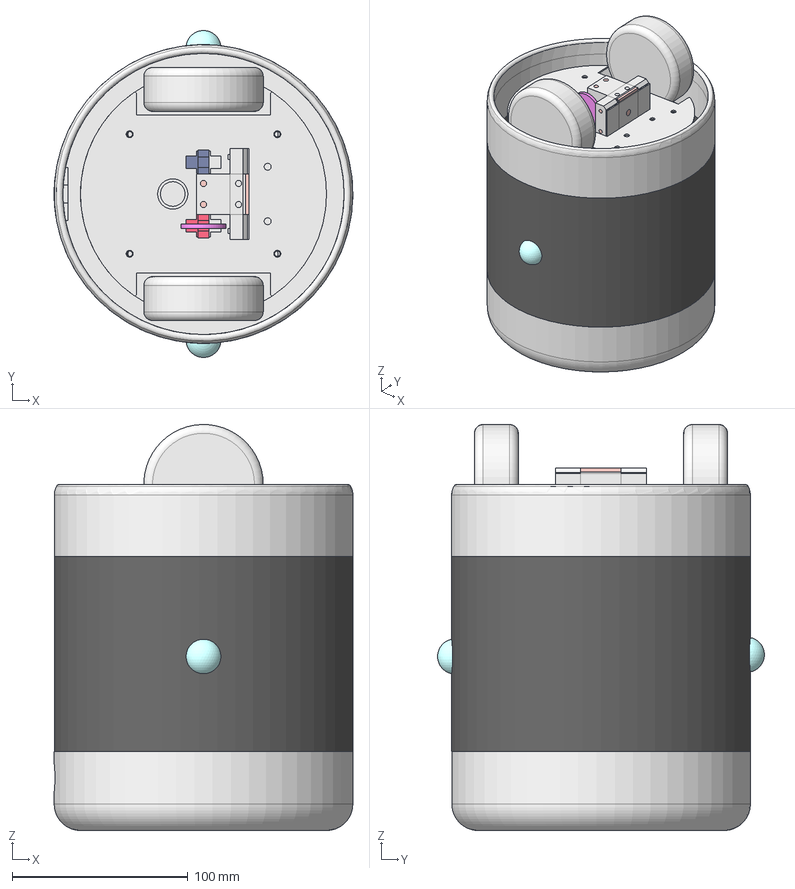
[picture p82: CAD file, 2024-08-18]
freecad/mrburger_chassis.FCStd
170.0 x 185.9 x 231.0 mm
encoder_disc
sensor
spacer
sensor001
bottom_plate
motor_holder
botom_spacers
mid_spacers
mid_plate_2
mid_plate
top_spacers
top_plate
top_spacers_hat
Zawartość003
Zawartość005
mid_body
turn_signal_L
turn_signal_R
wheel_L
wheel_R
inductive_coil_cap
