kamilkurach/mrburger/freecad/mrburger_top_plate_original.FCStd

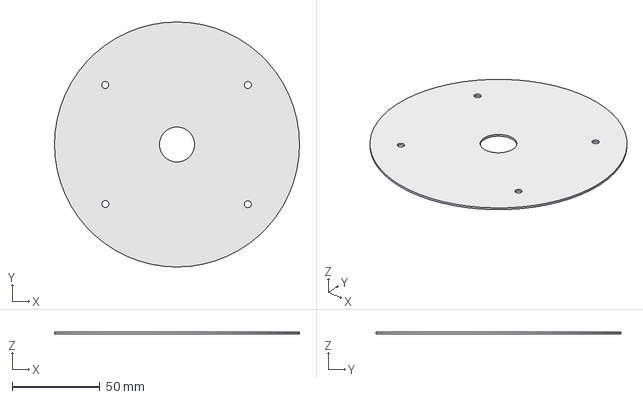
[picture p83: CAD file, 2024-08-12]
freecad/mrburger_top_plate_original.FCStd
140.0 x 140.0 x 1.10 mm
