kamilkurach/mrburger/freecad/mrburger_hat_light.FCStd

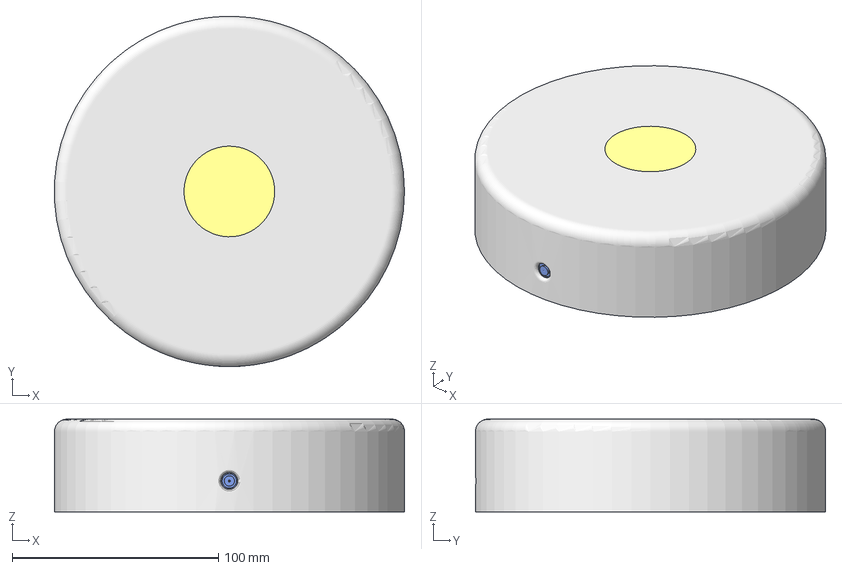
[picture p84: CAD file, 2024-08-11]
freecad/mrburger_hat_light.FCStd
169.9 x 170.0 x 45.0 mm
inductive_coil_cap
Zawartość002
Zawartość003
mrburger_camera_module
