kamilkurach/mrburger/freecad/mrburger_hat.FCStd

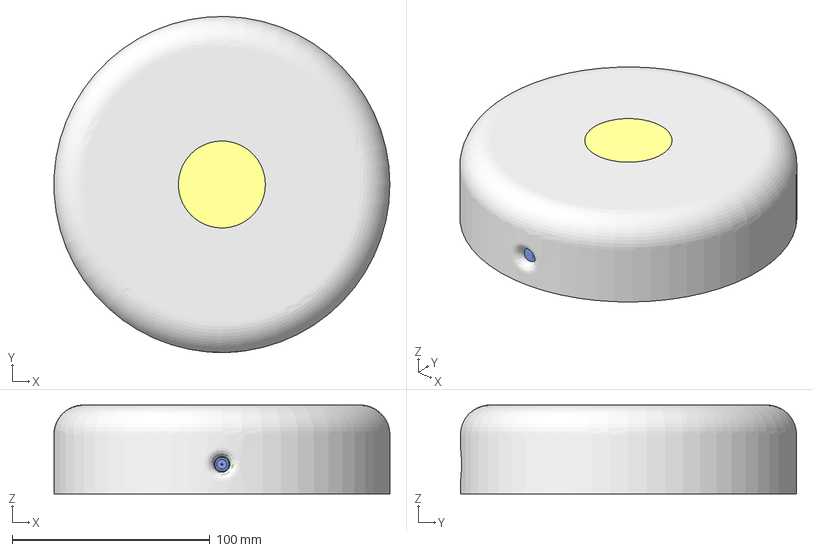
[picture p85: CAD file, 2024-08-11]
freecad/mrburger_hat.FCStd
169.9 x 170.0 x 45.0 mm
inductive_coil_cap
Zawartość003
mrburger_camera_module
