kamilkurach/mrburger/freecad/mrburger_camera_module.FCStd

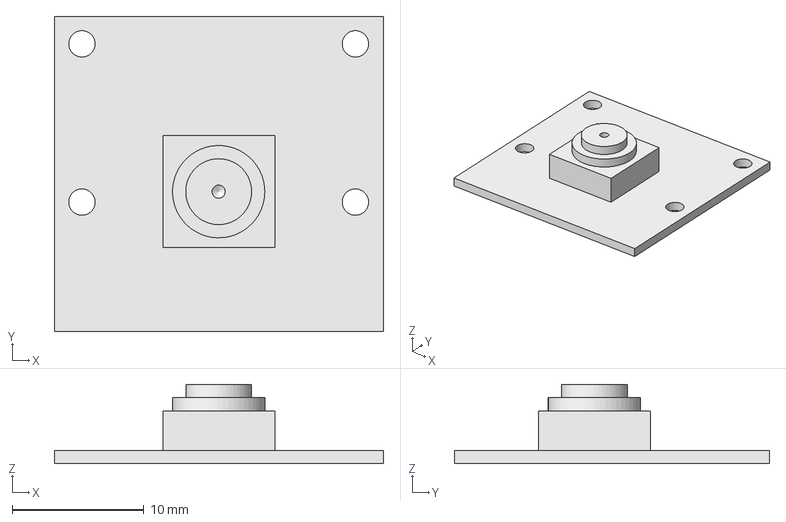
[picture p86: CAD file, 2024-08-11]
freecad/mrburger_camera_module.FCStd
24.9 x 23.9 x 6.00 mm
