kamilkurach/mrburger/freecad/mrburger_imu_pin.FCStd

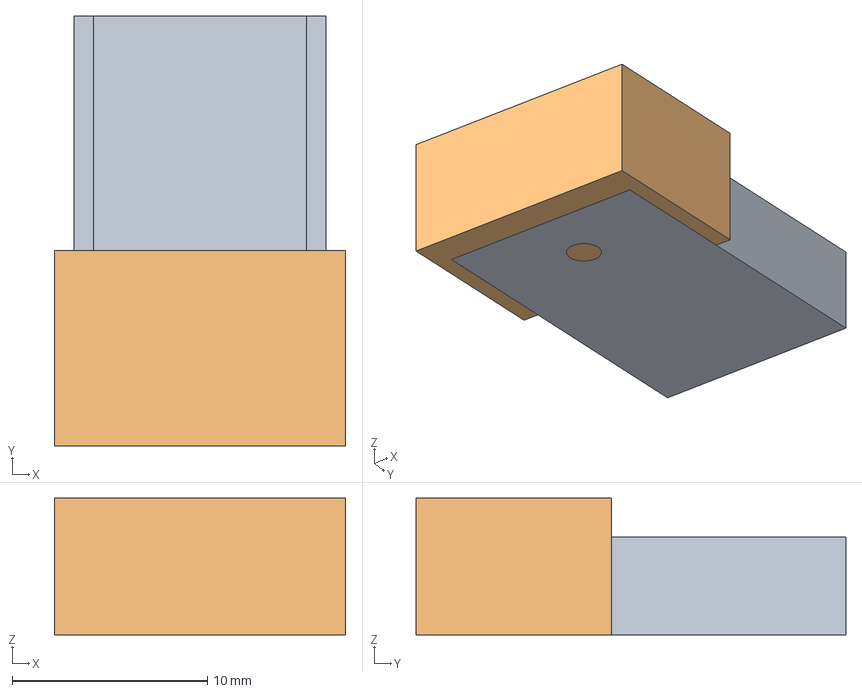
[picture p87: CAD file, 2024-08-09]
freecad/mrburger_imu_pin.FCStd
14.9 x 22.0 x 7.00 mm
Zawartość002
