kamilkurach/mrburger/freecad/mrburger_imu_mount.FCStd

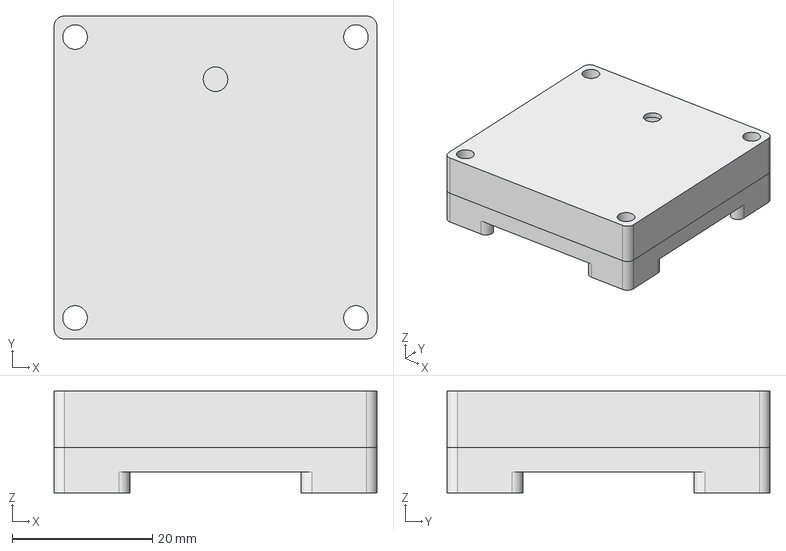
[picture p88: CAD file, 2024-08-08]
freecad/mrburger_imu_mount.FCStd
46.0 x 46.0 x 14.5 mm
top_cover
Zawartość002
bottom
