kamilkurach/mrburger/freecad/mrburger_imu.FCStd

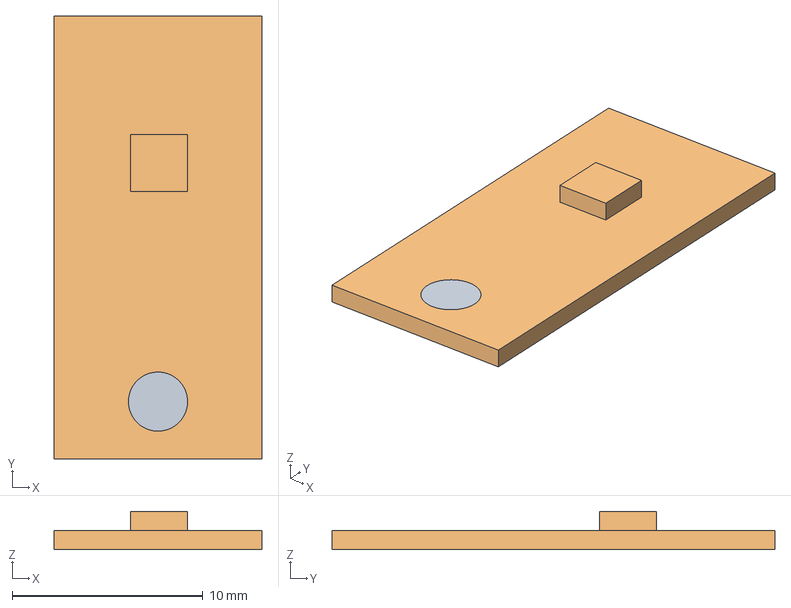
[picture p89: CAD file, 2024-08-08]
freecad/mrburger_imu.FCStd
10.9 x 23.2 x 2.00 mm
