kamilkurach/mrburger/freecad/mrburger_fan_inlet.FCStd

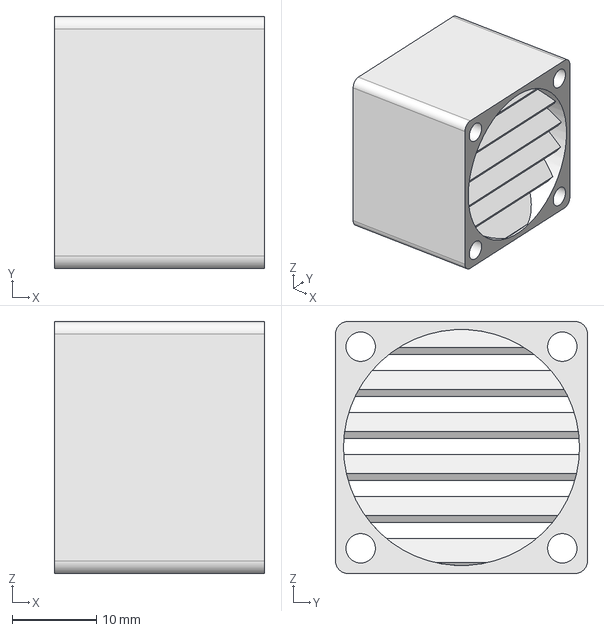
[picture p90: CAD file, 2024-08-06]
freecad/mrburger_fan_inlet.FCStd
25.0 x 30.0 x 30.0 mm
