kamilkurach/mrburger/freecad/mrburger_encoder_dust_cover_3.FCStd

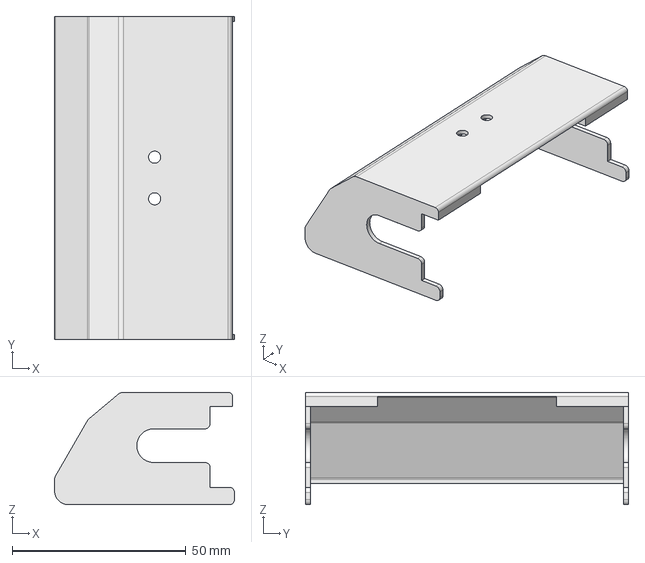
[picture p91: CAD file, 2024-08-03]
freecad/mrburger_encoder_dust_cover_3.FCStd
51.8 x 93.0 x 32.3 mm
