kamilkurach/mrburger/freecad/mrburger_encoder_dust_cover_2.FCStd

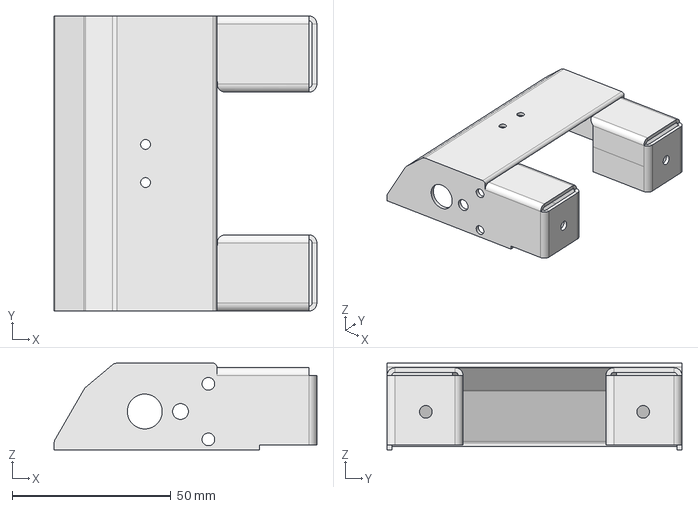
[picture p92: CAD file, 2024-07-31]
freecad/mrburger_encoder_dust_cover_2.FCStd
82.8 x 93.0 x 27.3 mm
