kamilkurach/mrburger/freecad/mrburger_encoder_spacer.FCStd

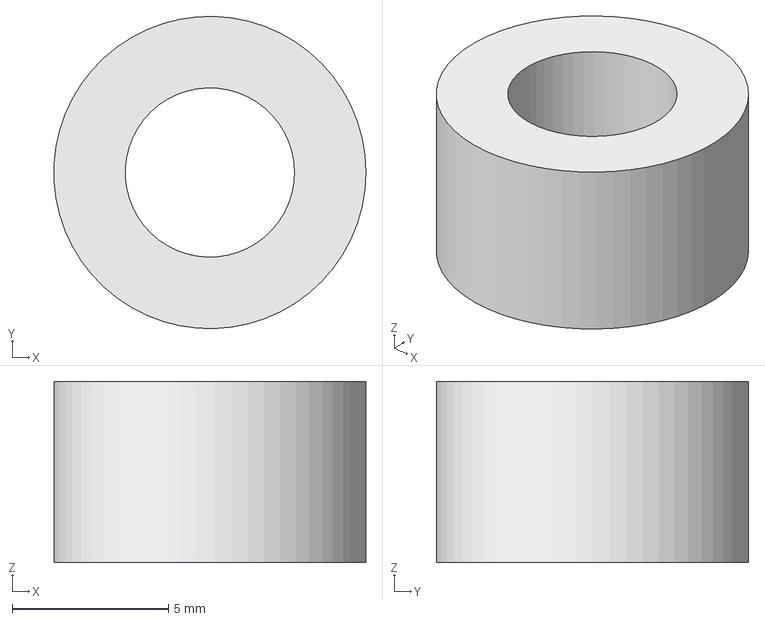
[picture p93: CAD file, 2024-07-30]
freecad/mrburger_encoder_spacer.FCStd
9.99 x 10.00 x 5.80 mm
