kamilkurach/mrburger/freecad/mrburger_encoder_dust_cover.FCStd

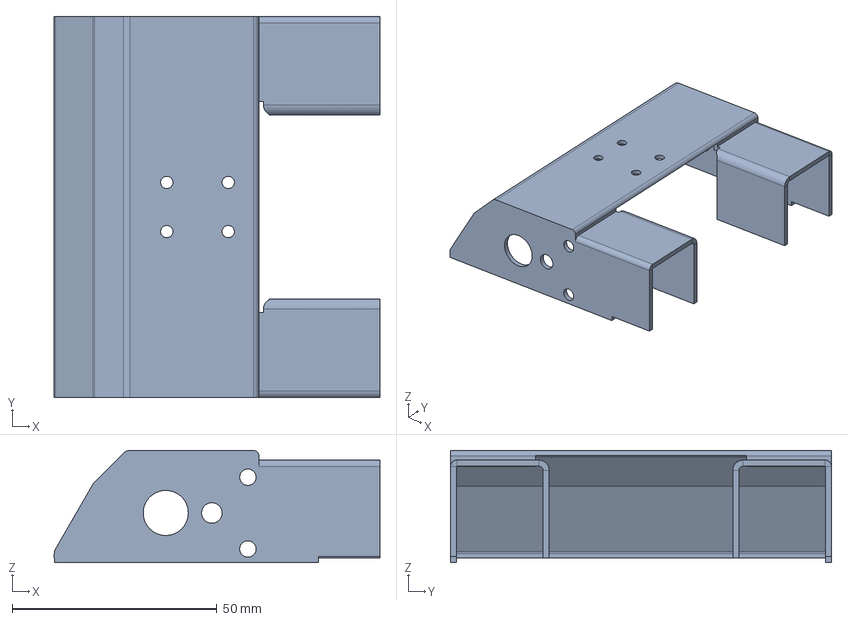
[picture p94: CAD file, 2024-07-30]
freecad/mrburger_encoder_dust_cover.FCStd
79.5 x 93.0 x 27.4 mm
