kamilkurach/mrburger/freecad/mrburger_sensor_holder.FCStd

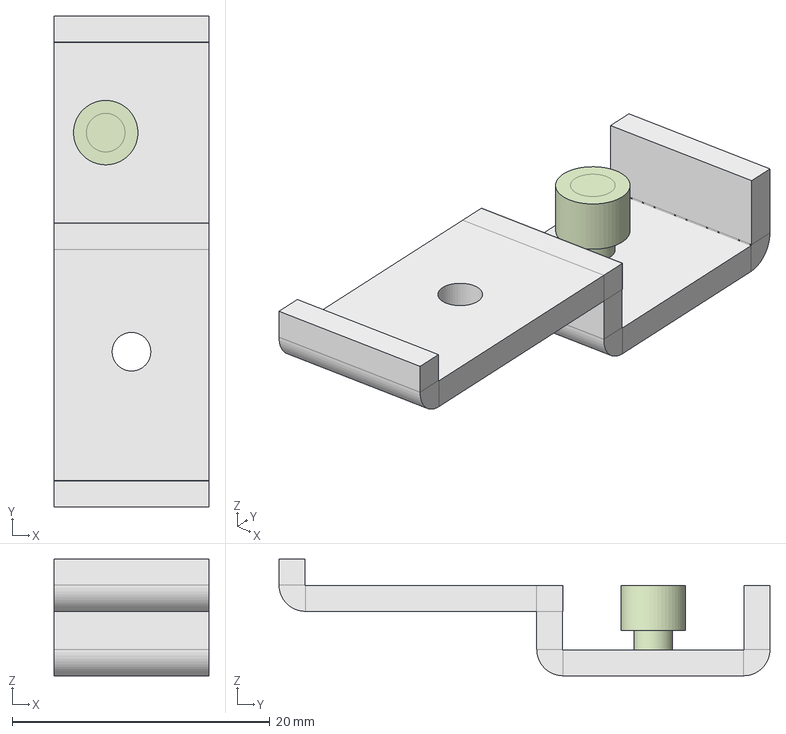
[picture p95: CAD file, 2024-07-21]
freecad/mrburger_sensor_holder.FCStd
12.0 x 38.1 x 9.05 mm
spacer
sensor_holder_right
