kamilkurach/mrburger/freecad/sensor.FCStd

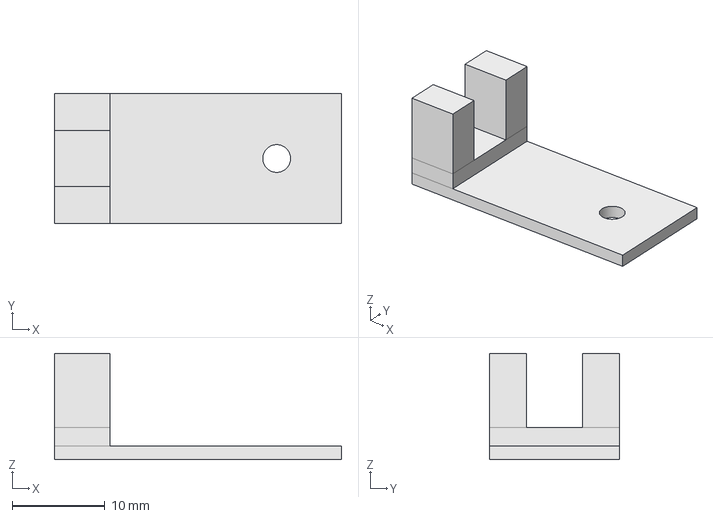
[picture p96: CAD file, 2024-07-21]
freecad/sensor.FCStd
31.0 x 14.0 x 11.5 mm
