kamilkurach/mrburger/kicad/mrburger_carrier_board/mrburger_carrier_board.kicad_pcb

## KiCad design schematics/logic-example.kicad_sch

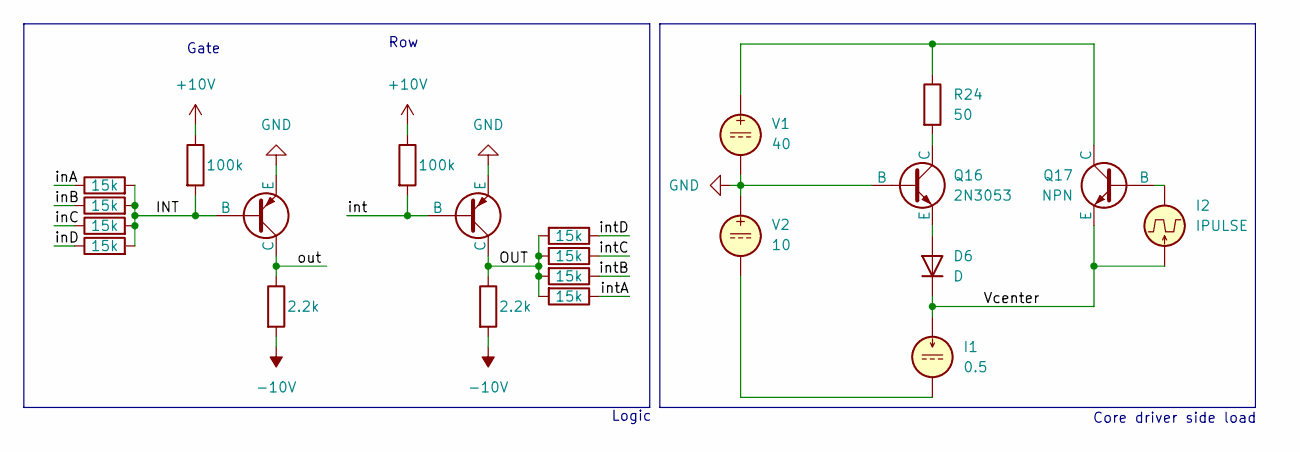
[picture p100: schematic logic-example.kicad_sch]

Parts:
D6: D
I1: 0.5
I2: IPULSE
Q14, Q15: PNP
Q16: 2N3053
Q17: NPN
R20, R22: 100k
R21, R23: 2.2k
R24: 50
R28, R29, R30, R31, R32, R33, R34, R35: 15k
V1: 40
V2: 10

Connections:
+10V: R20.1, R22.1
-10V: R21.2, R23.2
GND: Q14.3 (E), Q15.3 (E), Q16.2 (B), V1.2, V2.1
INT: Q14.2 (B), Q15.2 (B), R20.2, R22.2, R28.2, R29.2, R30.2, R31.2
unnamed: D6.2 (A), Q16.3 (E)
unnamed: I1.2, V2.2
unnamed: I2.2, Q17.2 (B)
unnamed: Q16.1 (C), R24.2
unnamed: Q17.1 (C), R24.1, V1.1
OUT: Q14.1 (C), Q15.1 (C), R21.1, R23.1, R32.2, R33.2, R34.2, R35.2
Vcenter: D6.1 (K), I1.1, I2.1, Q17.3 (E)
inA: R28.1
inB: R29.1
inC: R30.1
inD: R31.1
intA: R32.1
intB: R33.1
intC: R34.1
intD: R35.1

Notes on the sheet:
Core driver side load
Logic
Gate
Row
