kamilkurach/mrburger/scripts/client.py

import socket
import keyboard

host = '192.168.5.111'
socket = socket.socket(socket.AF_INET, socket.SOCK_STREAM)
socket.connect((host, 8080))

while True:
  if keyboard.read_key() == 'w':
    s = 'w'
    s_encode = s.encode()
    socket.send(s_encode)
    print('\n')
  elif keyboard.read_key() == 'x':
    s = 'x'
    s_encode = s.encode()
    socket.send(s_encode)
    print('\n')
  elif keyboard.read_key() == 's':
    s = 's'
    s_encode = s.encode()
    socket.send(s_encode)
    print('\n')
  elif keyboard.read_key() == 'a':
    s = 'a'
    s_encode = s.encode()
    socket.send(s_encode)
    print('\n')
  elif keyboard.read_key() == 'd':
    s = 'd'
    s_encode = s.encode()
    socket.send(s_encode)
    print('\n')
  elif keyboard.read_key() == 'r':
    s = 'r'
    s_encode = s.encode()
    socket.send(s_encode)
    print('\n')
  elif keyboard.read_key() == 'l':
    s = 'l'
    s_encode = s.encode()
    socket.send(s_encode)
    print('\n')
  elif keyboard.read_key() == 'q':
    s = 'q'
    s_encode = s.encode()
    socket.send(s_encode)
    print('\n')
    socket.close()
    break
  elif keyboard.read_key() == 'b':
    s = 'b'
    s_encode = s.encode()
    socket.send(s_encode)
    print('\n')
